brandonhippe/Indoor-Air-Quality-Monitor/Google Drive/Pin Definitions.docx

Unchangeable Pins:

- I2C_0 SCL: 9
- I2C_0 SDA: 10
- I2C_1 SCL: 14
- I2C_1 SDA: 15
- RX: 3
- TX: 4

Changeable Pins:

- PM_SLEEP_PIN: 6
- CO2_SLEEP_PIN: 7
- ANEM_SLEEP_PIN: 8
- ULTRASONIC_TRIG_1: 16
- ULTRASONIC_ECHO_1: 17
- ULTRASONIC_TRIG_2: 18
- ULTRASONIC_ECHO_2: 19
- Manny please put changeable smartmesh pins here

Notes:

- Sleep pins should have spots for transistors to turn off that sensor. Not likely to need them all, but probably nice to have
- Likely will need 2nd I2C bus for just CO2 sensor in order to properly put it to sleep without messing with other sensors on bus

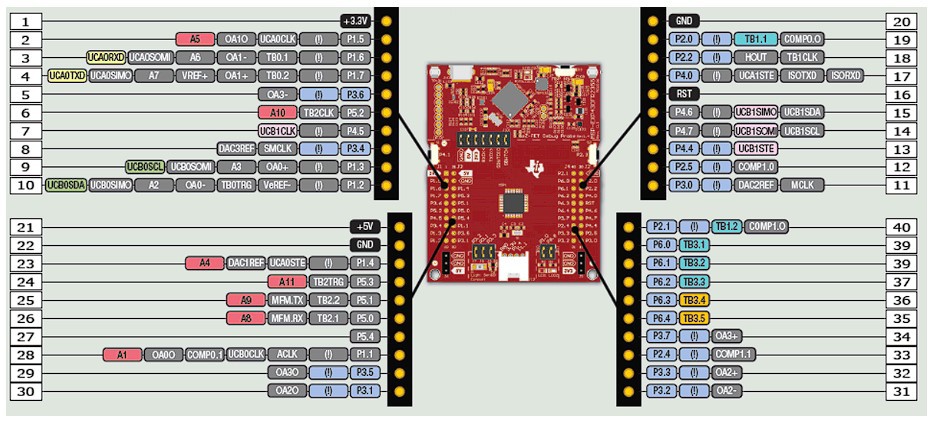
[picture p56: figure]
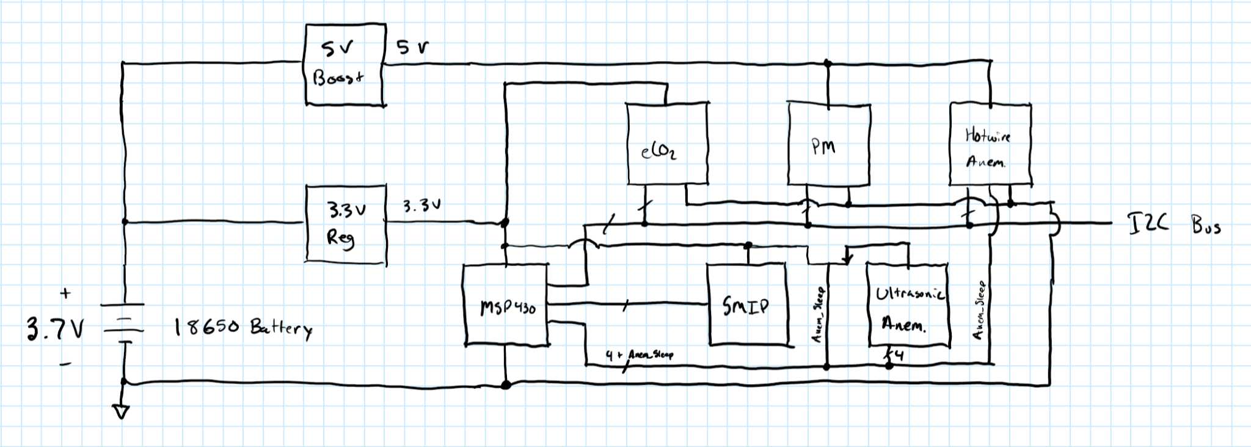
[picture p57: figure]
