brandonhippe/Indoor-Air-Quality-Monitor/Google Drive/Photos/COM port selected.png

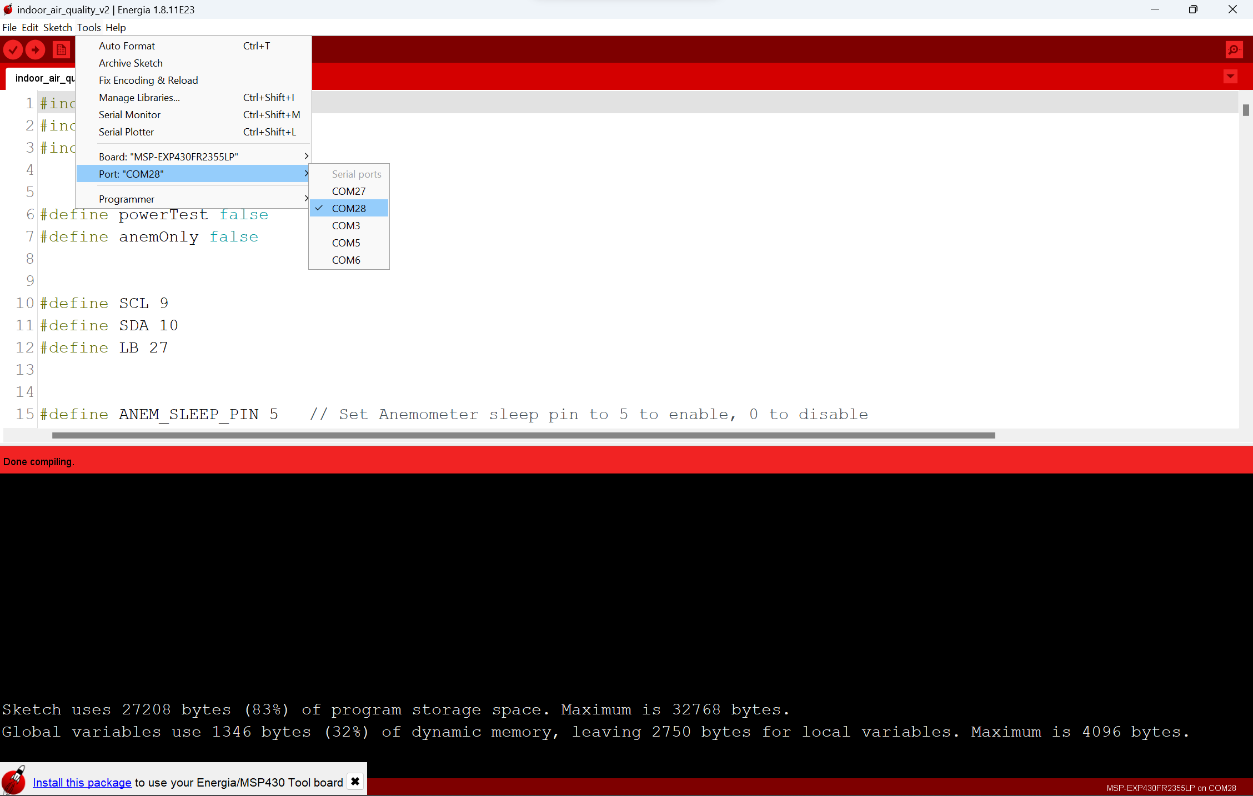
Google Drive/Photos/COM port selected.png
