brandonhippe/Indoor-Air-Quality-Monitor/Google Drive/Photos/device manager.png

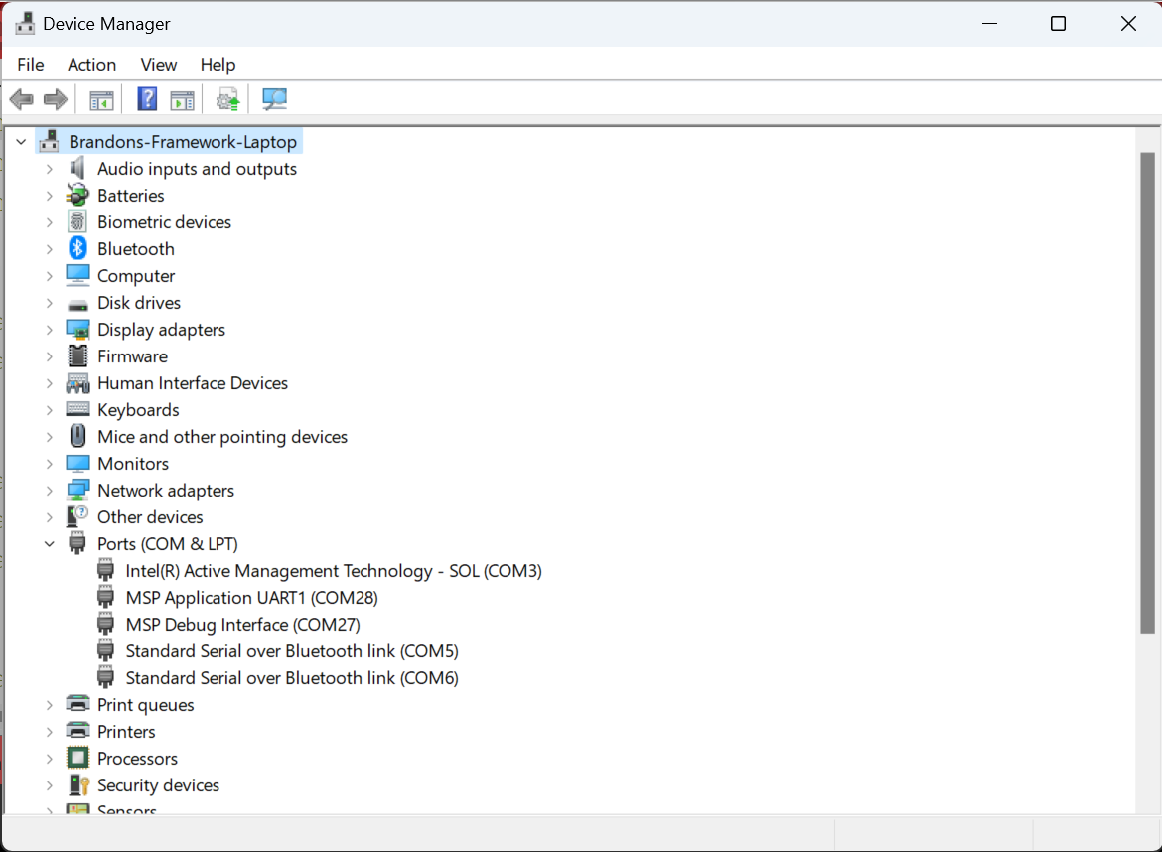
Google Drive/Photos/device manager.png
