brandonhippe/Indoor-Air-Quality-Monitor/Google Drive/Photos/Energia Started and board selected.png

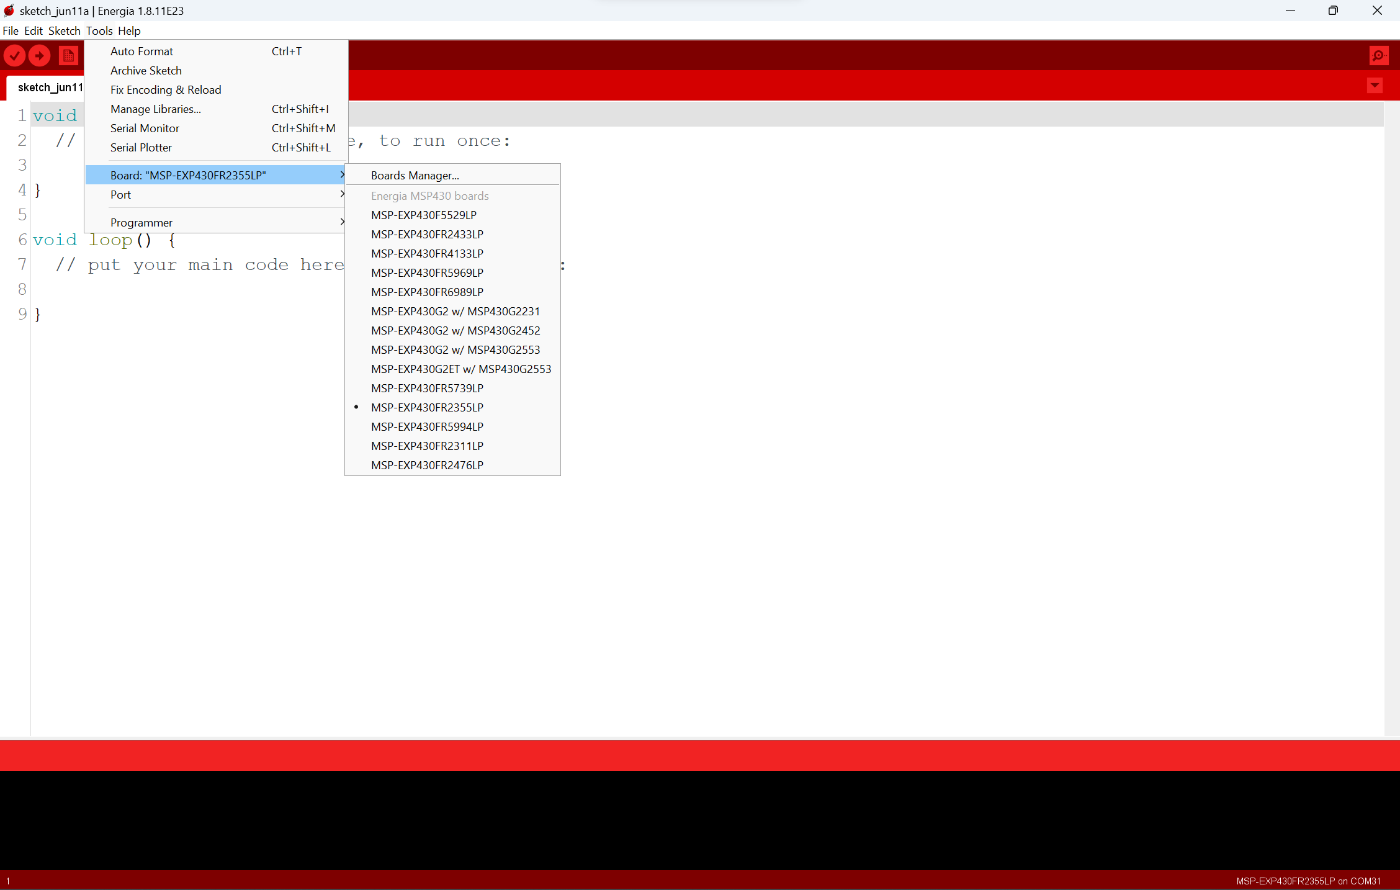
Google Drive/Photos/Energia Started and board selected.png
