brandonhippe/Indoor-Air-Quality-Monitor/Google Drive/Photos/Github Download.png

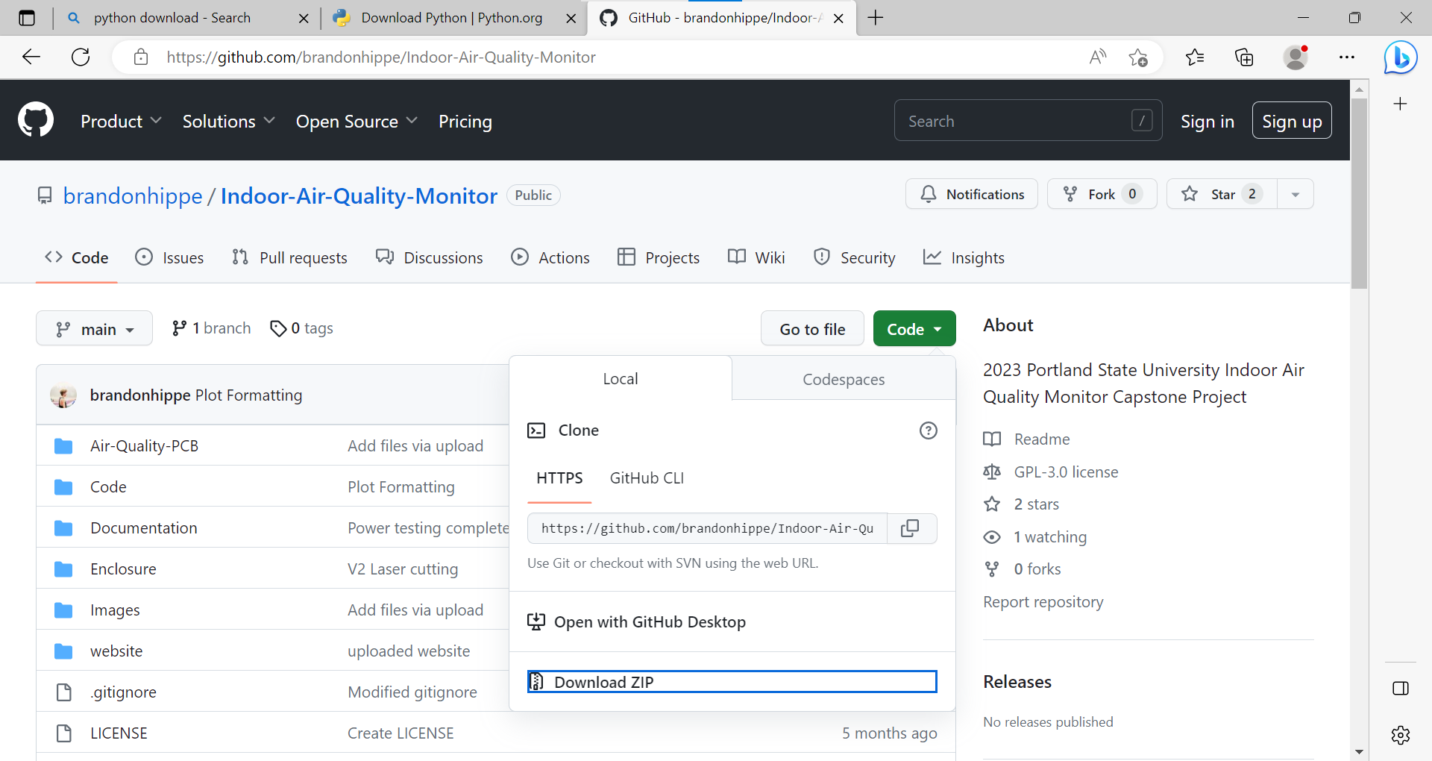
Google Drive/Photos/Github Download.png
