brandonhippe/Indoor-Air-Quality-Monitor/Google Drive/Photos/Libraries copied.png

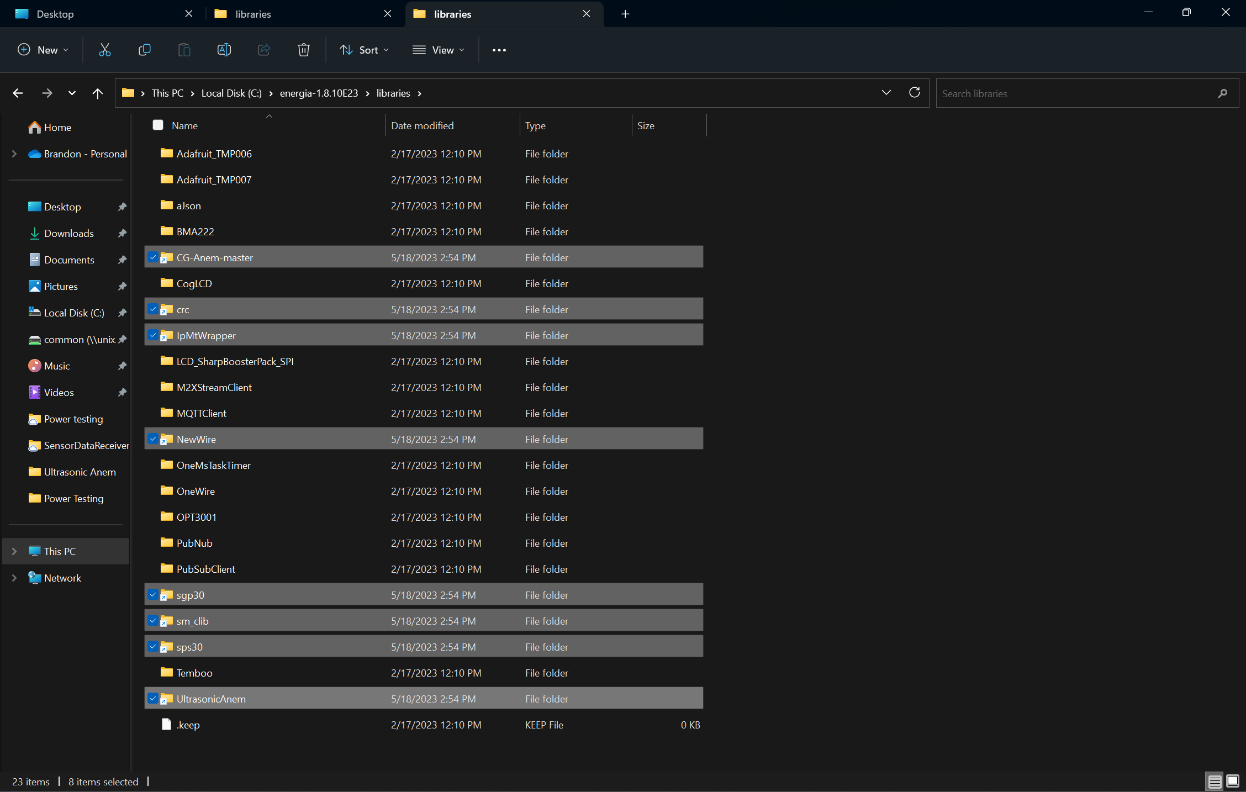
Google Drive/Photos/Libraries copied.png
