brandonhippe/Indoor-Air-Quality-Monitor/Google Drive/Photos/Libraries to copy.png

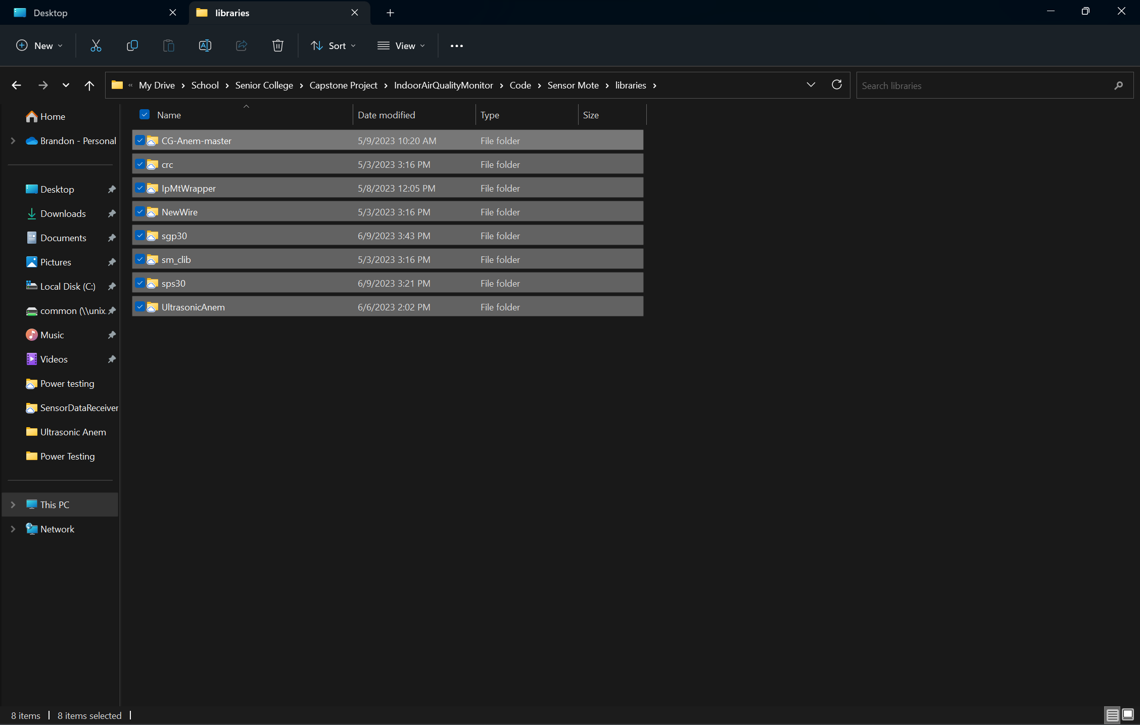
Google Drive/Photos/Libraries to copy.png
