brandonhippe/Indoor-Air-Quality-Monitor/Google Drive/Photos/Low Battery Alert.png

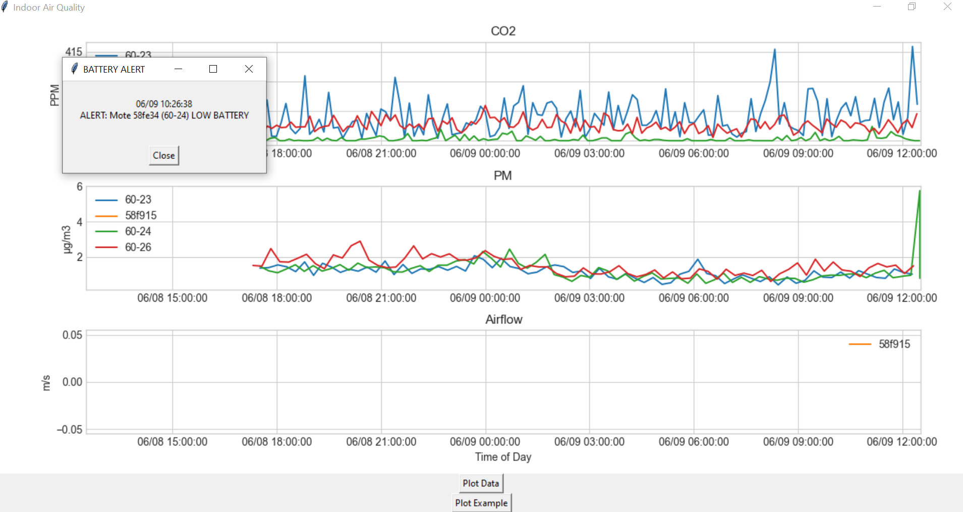
Google Drive/Photos/Low Battery Alert.png
