brandonhippe/Indoor-Air-Quality-Monitor/Google Drive/Photos/manager plugged in.png

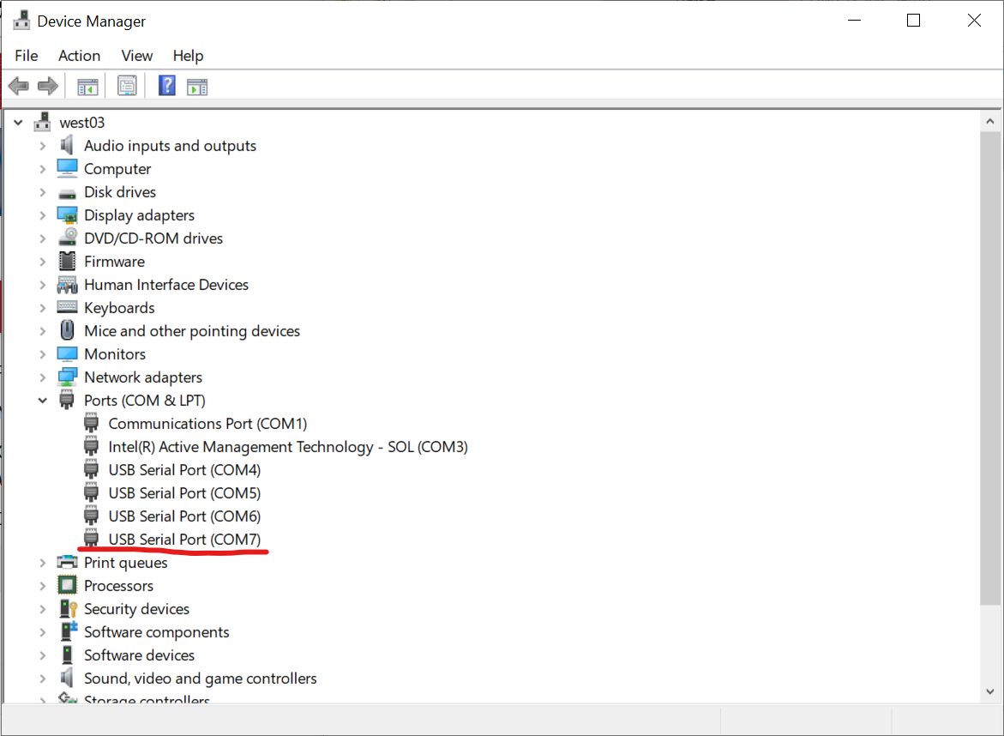
Google Drive/Photos/manager plugged in.png
