brandonhippe/Indoor-Air-Quality-Monitor/Google Drive/Photos/PXL_20230509_195835408.jpg

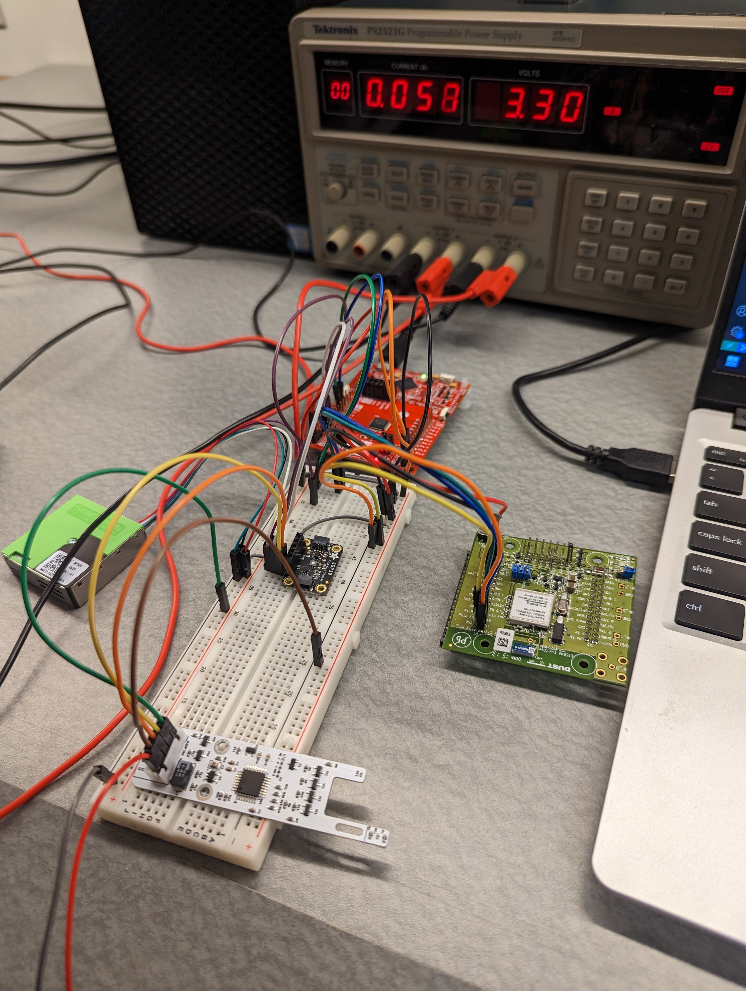
Google Drive/Photos/PXL_20230509_195835408.jpg
