brandonhippe/Indoor-Air-Quality-Monitor/Google Drive/Photos/PXL_20230510_175557905.jpg

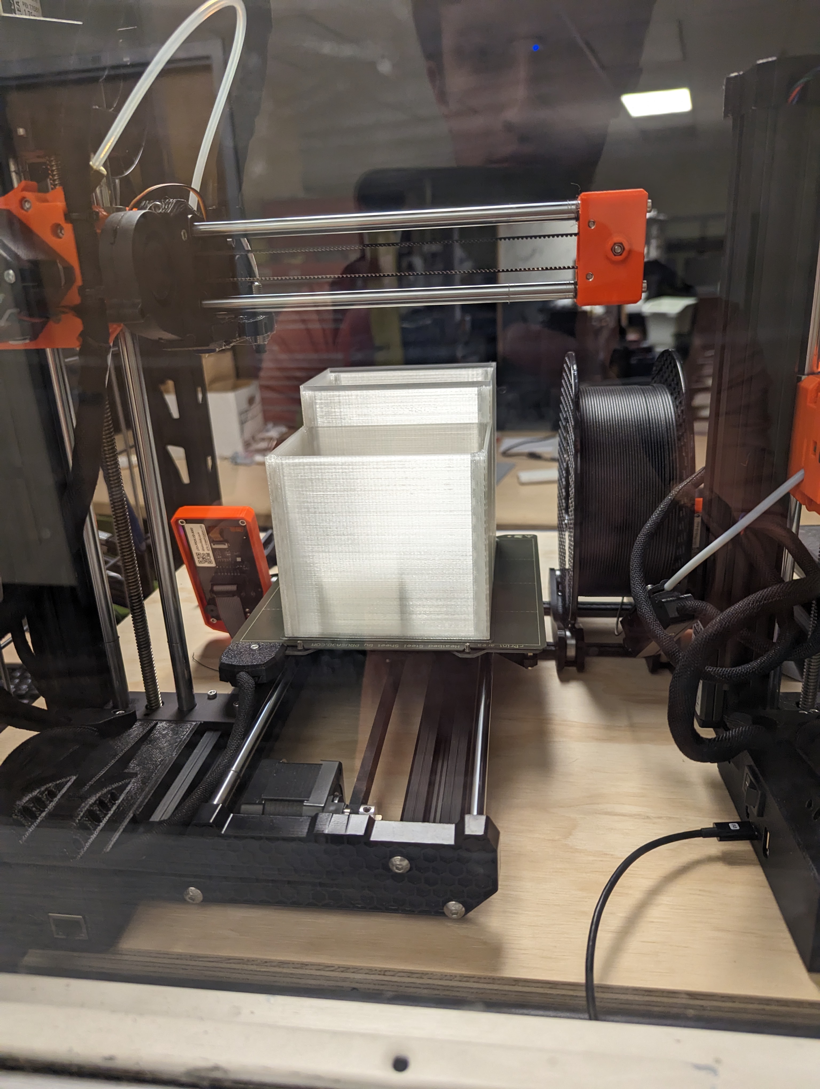
Google Drive/Photos/PXL_20230510_175557905.jpg
