brandonhippe/Indoor-Air-Quality-Monitor/Google Drive/Photos/PXL_20230510_200031936.jpg

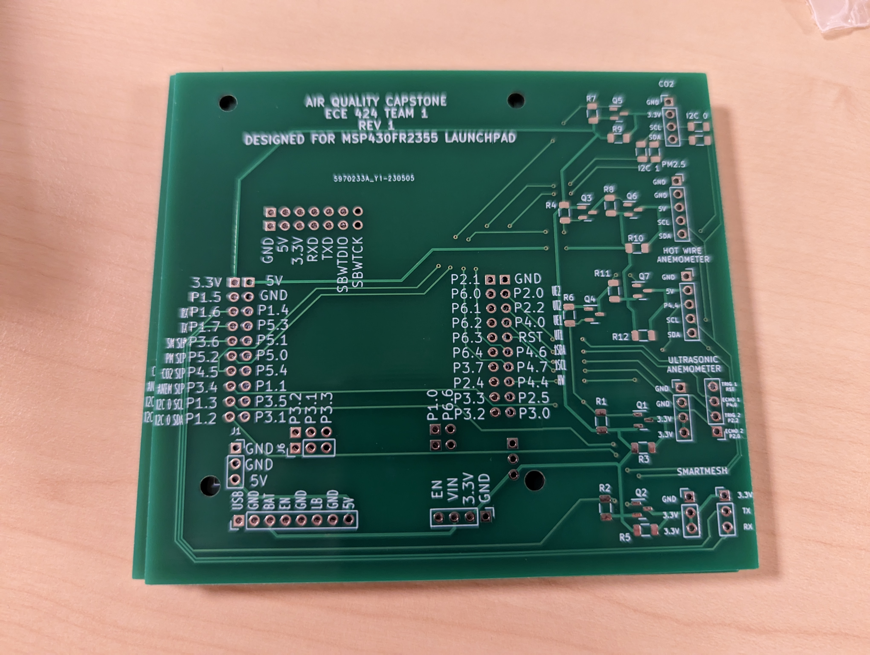
Google Drive/Photos/PXL_20230510_200031936.jpg
