brandonhippe/Indoor-Air-Quality-Monitor/Google Drive/Photos/PXL_20230516_212648805.jpg

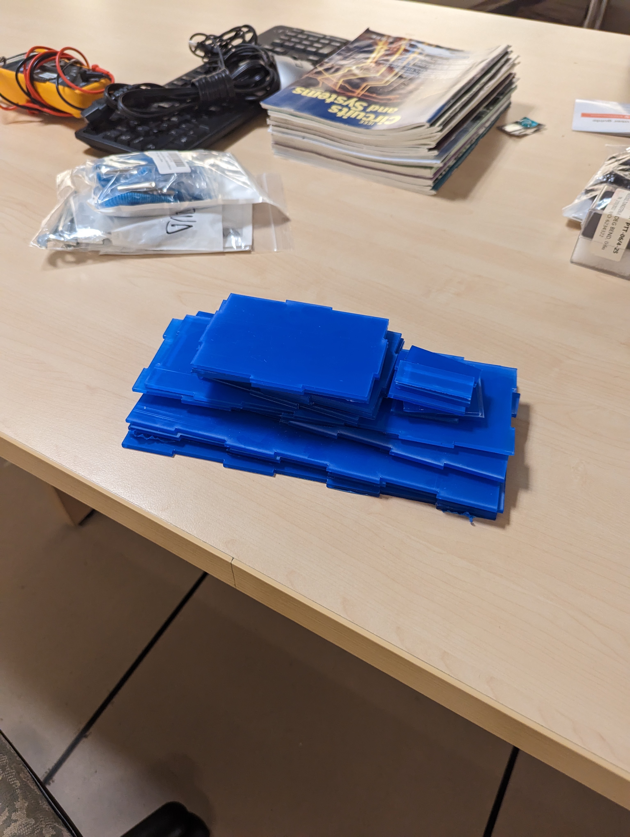
Google Drive/Photos/PXL_20230516_212648805.jpg
