brandonhippe/Indoor-Air-Quality-Monitor/Google Drive/Photos/PXL_20230516_223832451.jpg

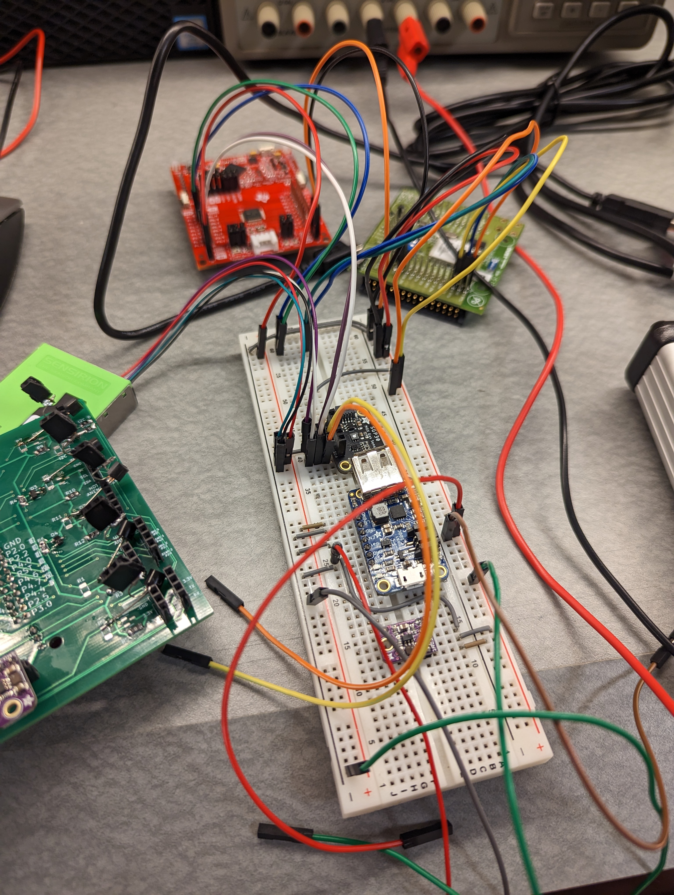
Google Drive/Photos/PXL_20230516_223832451.jpg
