brandonhippe/Indoor-Air-Quality-Monitor/Google Drive/Photos/PXL_20230524_002447540.jpg

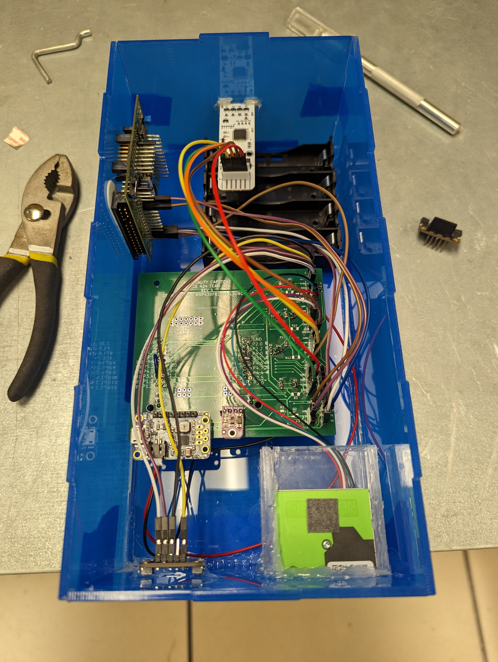
Google Drive/Photos/PXL_20230524_002447540.jpg
