brandonhippe/Indoor-Air-Quality-Monitor/Google Drive/Photos/PXL_20230524_012021392.jpg

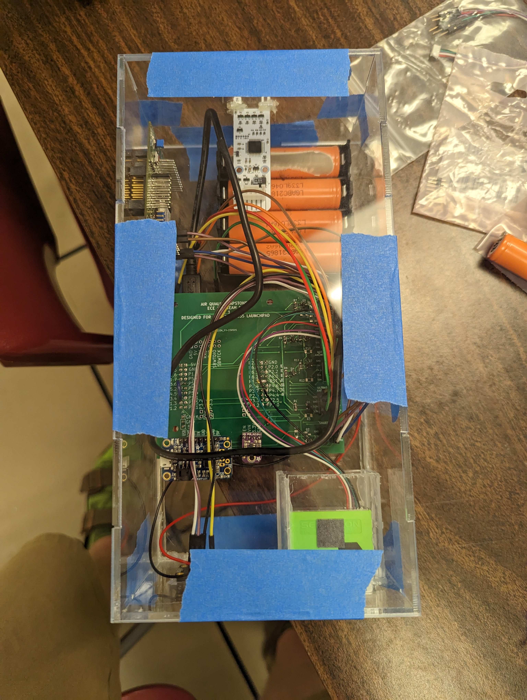
Google Drive/Photos/PXL_20230524_012021392.jpg
