brandonhippe/Indoor-Air-Quality-Monitor/Google Drive/Photos/PXL_20230524_172544205.jpg

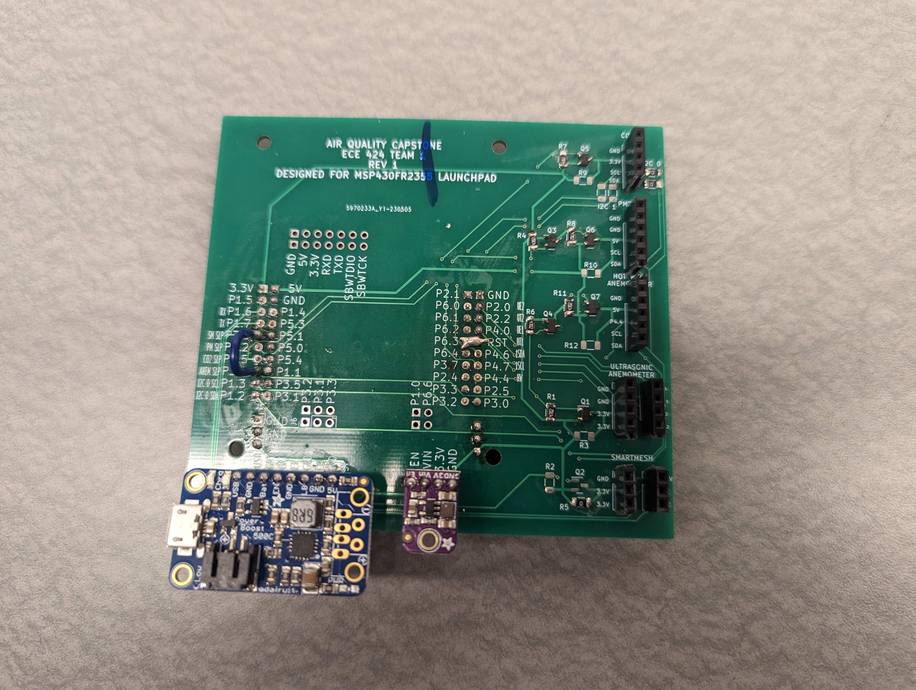
Google Drive/Photos/PXL_20230524_172544205.jpg
