brandonhippe/Indoor-Air-Quality-Monitor/Google Drive/Photos/PXL_20230524_172617568.jpg

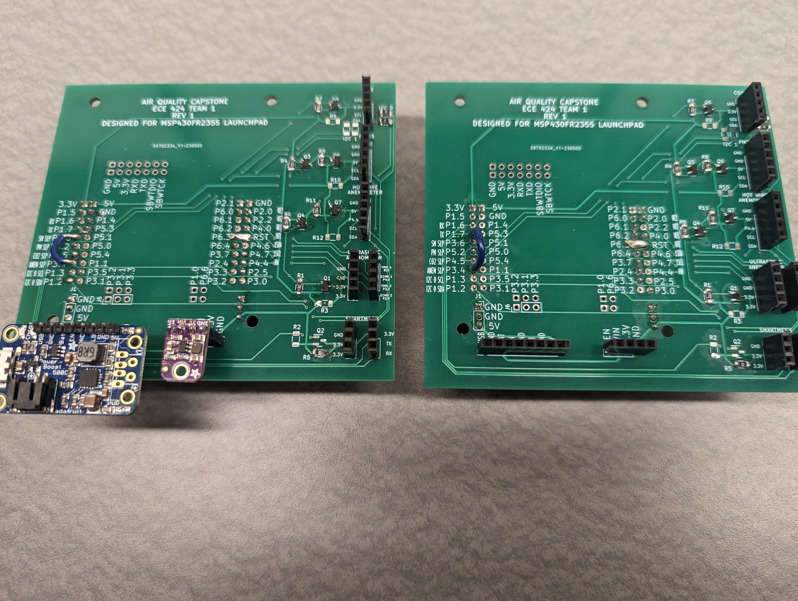
Google Drive/Photos/PXL_20230524_172617568.jpg
