brandonhippe/Indoor-Air-Quality-Monitor/Google Drive/Photos/PXL_20230524_172642097.jpg

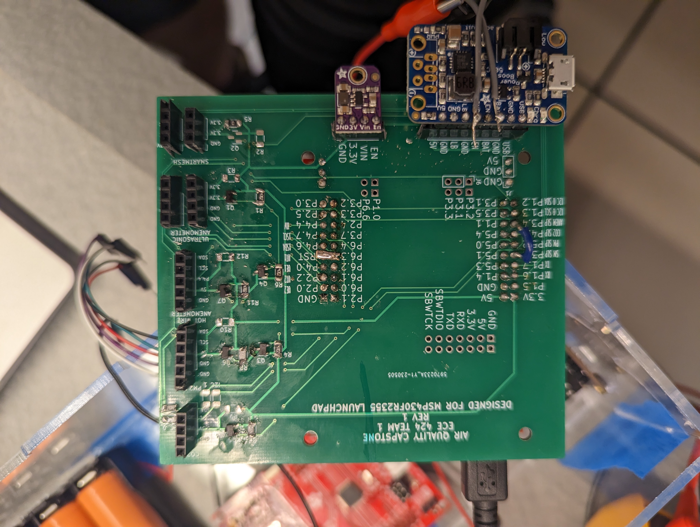
Google Drive/Photos/PXL_20230524_172642097.jpg
