brandonhippe/Indoor-Air-Quality-Monitor/Google Drive/Photos/PXL_20230602_221326991.jpg

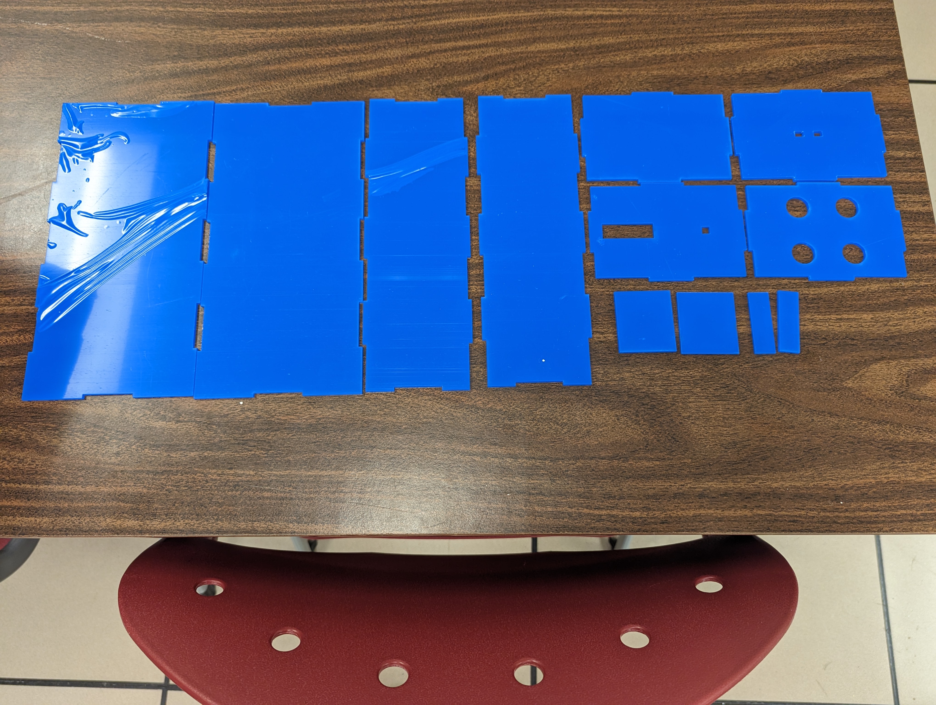
Google Drive/Photos/PXL_20230602_221326991.jpg
