brandonhippe/Indoor-Air-Quality-Monitor/Google Drive/Photos/PXL_20230602_222331544.jpg

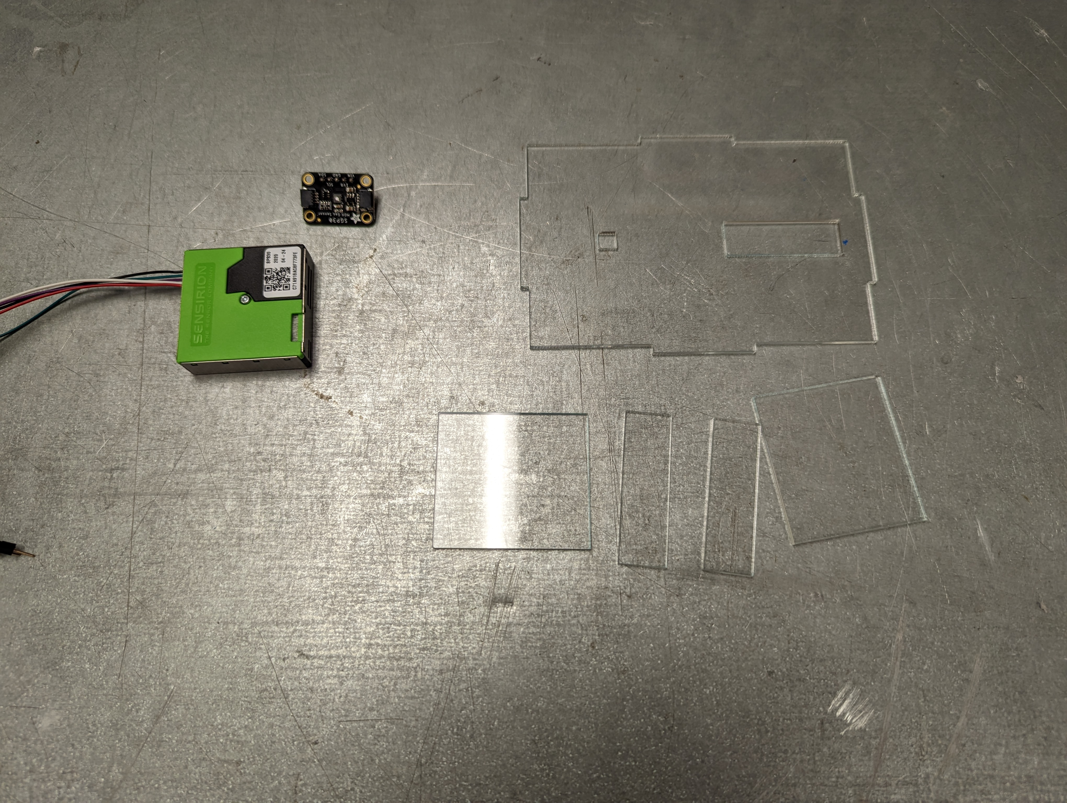
Google Drive/Photos/PXL_20230602_222331544.jpg
