brandonhippe/Indoor-Air-Quality-Monitor/Google Drive/Photos/PXL_20230602_222806239.jpg

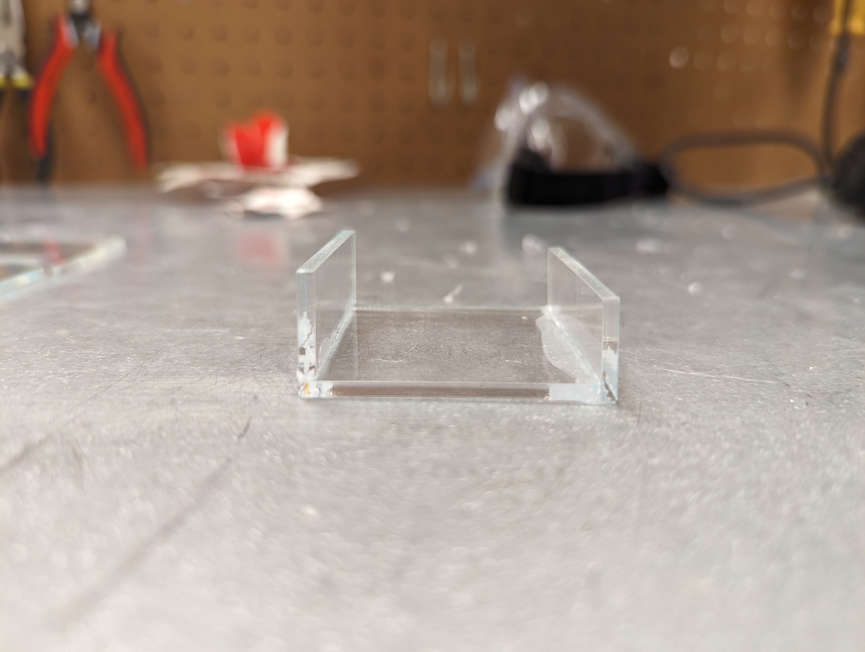
Google Drive/Photos/PXL_20230602_222806239.jpg
