brandonhippe/Indoor-Air-Quality-Monitor/Google Drive/Photos/PXL_20230602_222922491.jpg

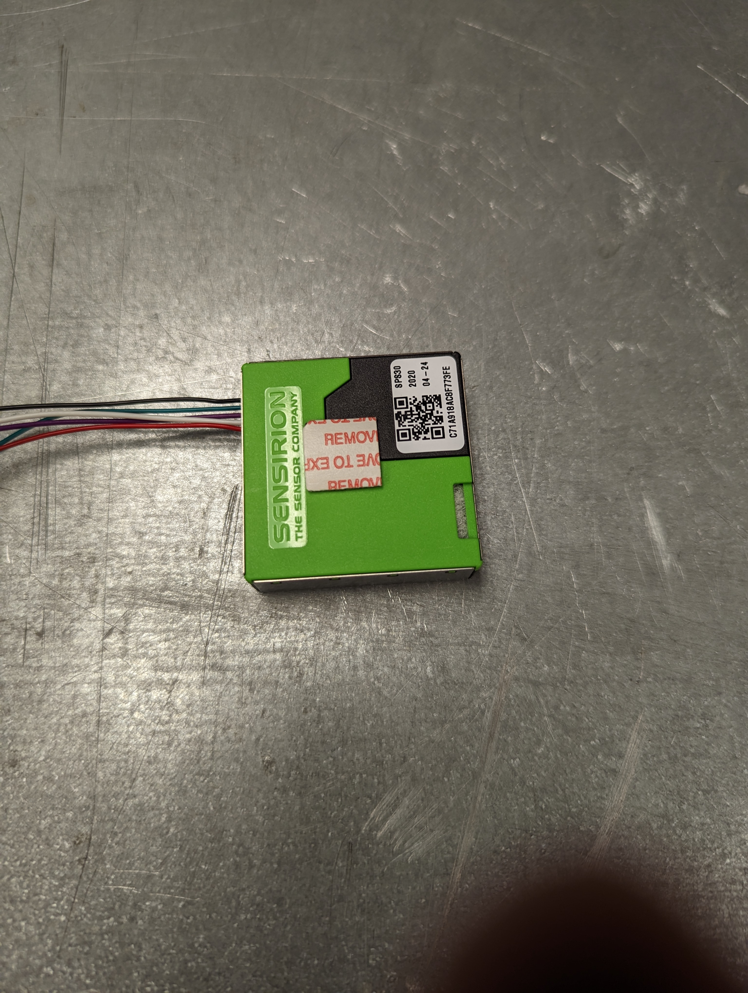
Google Drive/Photos/PXL_20230602_222922491.jpg
