brandonhippe/Indoor-Air-Quality-Monitor/Google Drive/Photos/PXL_20230602_223028937.jpg

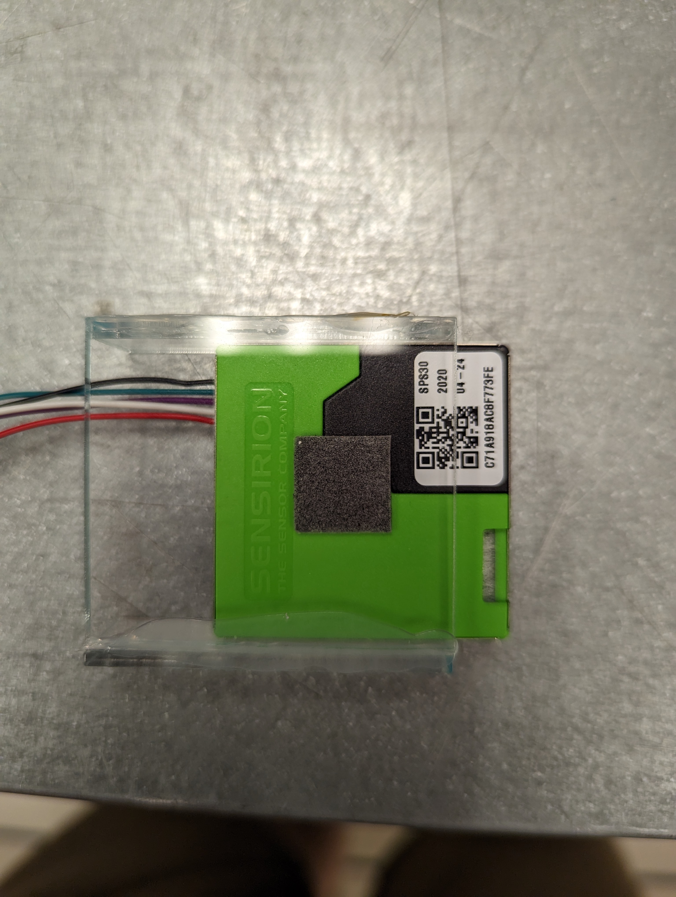
Google Drive/Photos/PXL_20230602_223028937.jpg
