brandonhippe/Indoor-Air-Quality-Monitor/Google Drive/Photos/PXL_20230602_223123664.jpg

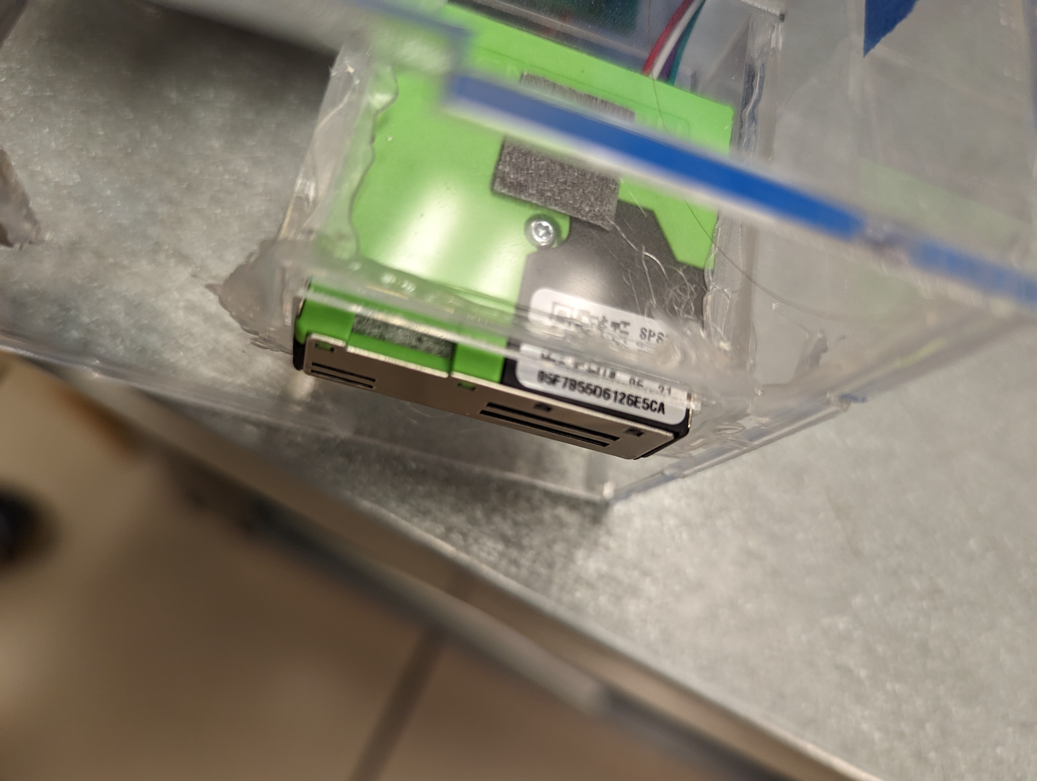
Google Drive/Photos/PXL_20230602_223123664.jpg
