brandonhippe/Indoor-Air-Quality-Monitor/Google Drive/Photos/PXL_20230602_223311003.jpg

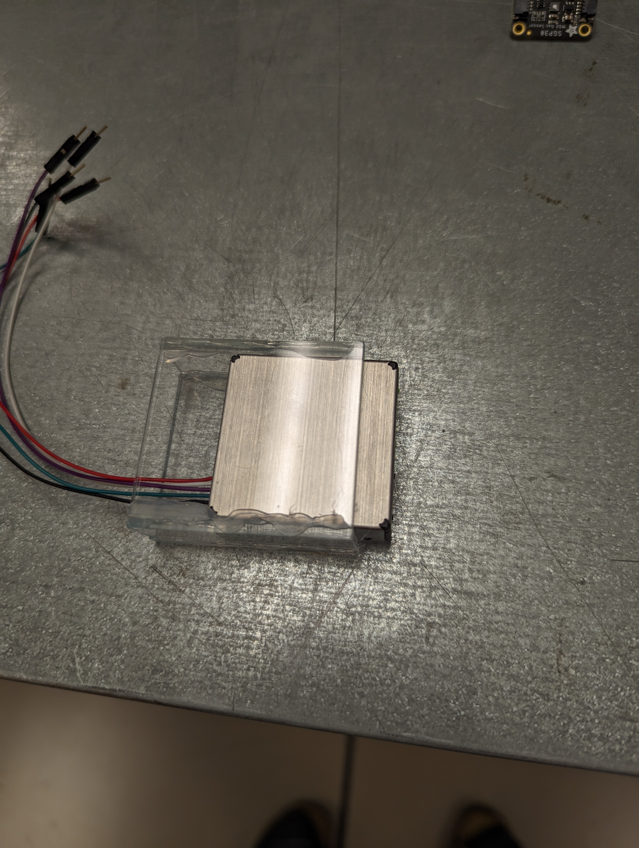
Google Drive/Photos/PXL_20230602_223311003.jpg
