brandonhippe/Indoor-Air-Quality-Monitor/Google Drive/Photos/PXL_20230602_223421171.jpg

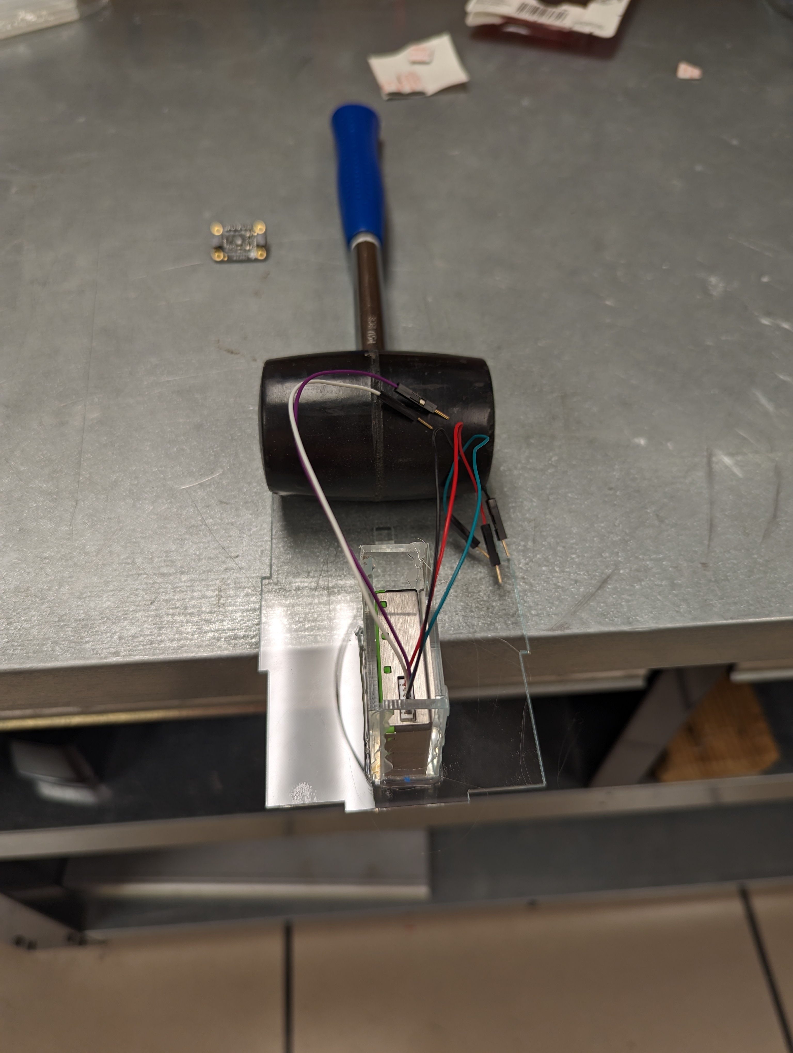
Google Drive/Photos/PXL_20230602_223421171.jpg
