brandonhippe/Indoor-Air-Quality-Monitor/Google Drive/Photos/PXL_20230602_223711670.jpg

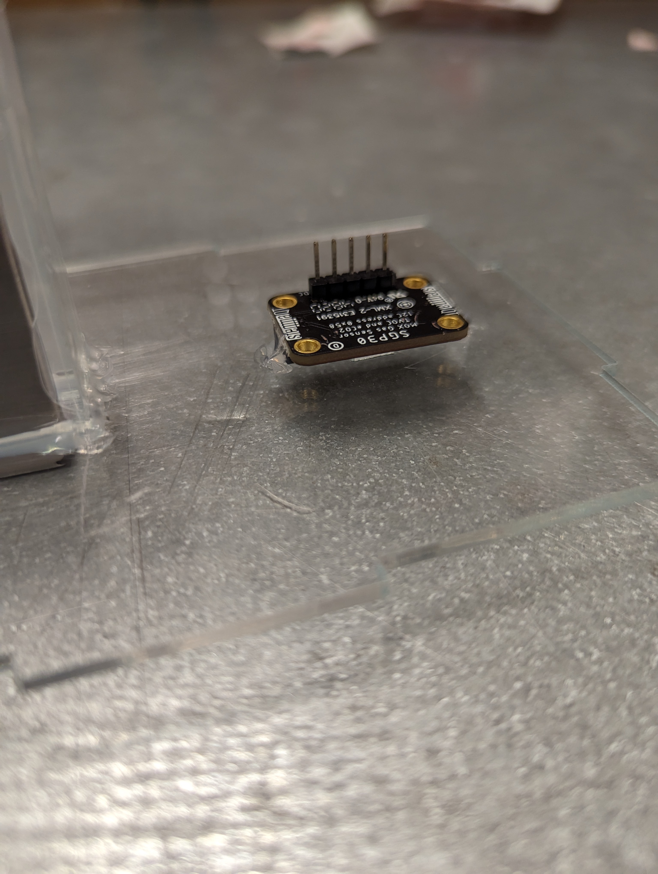
Google Drive/Photos/PXL_20230602_223711670.jpg
