brandonhippe/Indoor-Air-Quality-Monitor/Google Drive/Photos/PXL_20230602_223719457.jpg

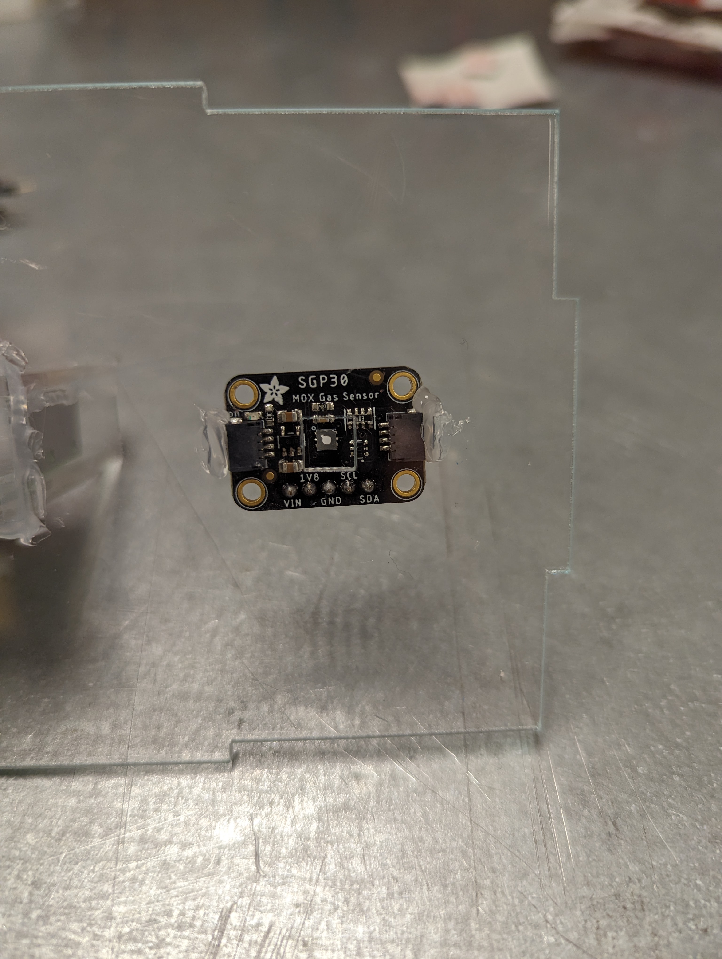
Google Drive/Photos/PXL_20230602_223719457.jpg
