brandonhippe/Indoor-Air-Quality-Monitor/Google Drive/Photos/PXL_20230602_224345984.jpg

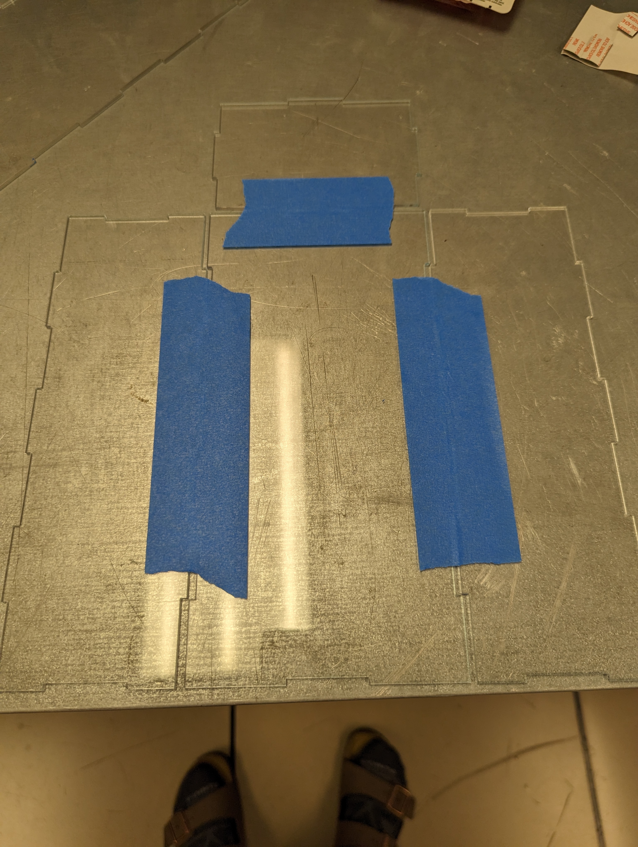
Google Drive/Photos/PXL_20230602_224345984.jpg
