brandonhippe/Indoor-Air-Quality-Monitor/Google Drive/Photos/PXL_20230602_224513106.jpg

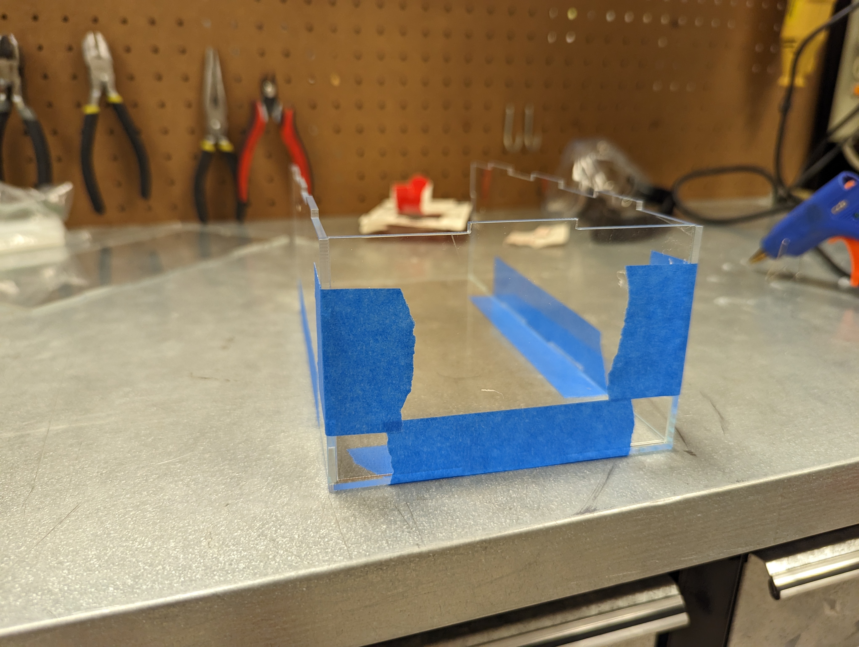
Google Drive/Photos/PXL_20230602_224513106.jpg
