brandonhippe/Indoor-Air-Quality-Monitor/Google Drive/Photos/PXL_20230602_225319473.jpg

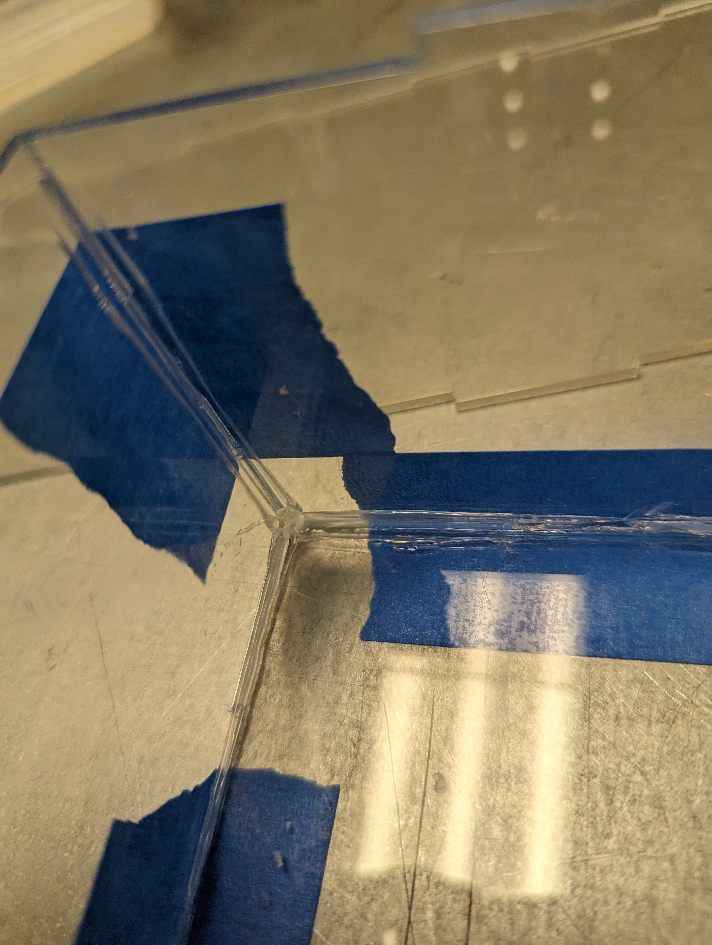
Google Drive/Photos/PXL_20230602_225319473.jpg
