brandonhippe/Indoor-Air-Quality-Monitor/Google Drive/Photos/PXL_20230602_225957423.jpg

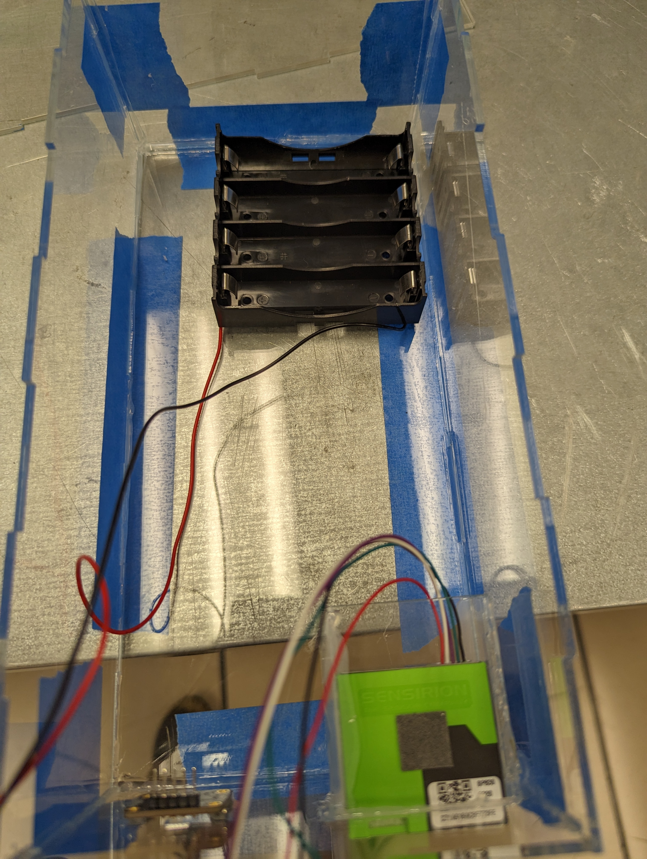
Google Drive/Photos/PXL_20230602_225957423.jpg
