brandonhippe/Indoor-Air-Quality-Monitor/Google Drive/Photos/PXL_20230602_230428449.jpg

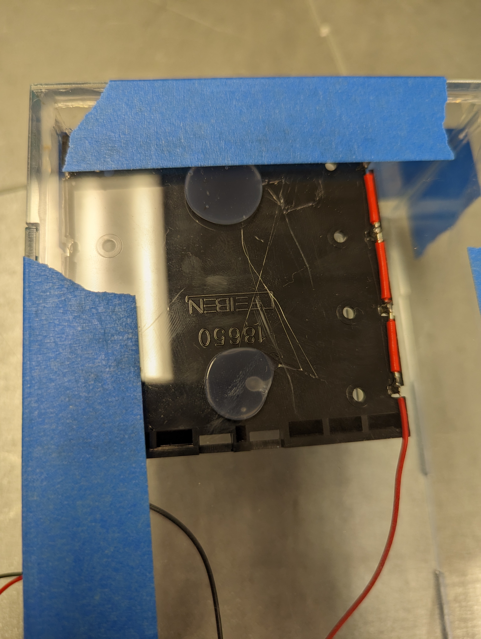
Google Drive/Photos/PXL_20230602_230428449.jpg
