brandonhippe/Indoor-Air-Quality-Monitor/Google Drive/Photos/PXL_20230602_230817055.jpg

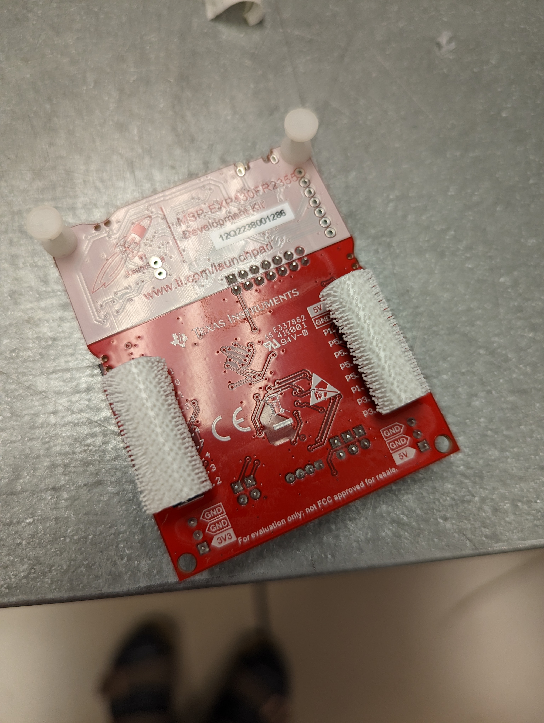
Google Drive/Photos/PXL_20230602_230817055.jpg
