brandonhippe/Indoor-Air-Quality-Monitor/Google Drive/Photos/PXL_20230602_230912100.jpg

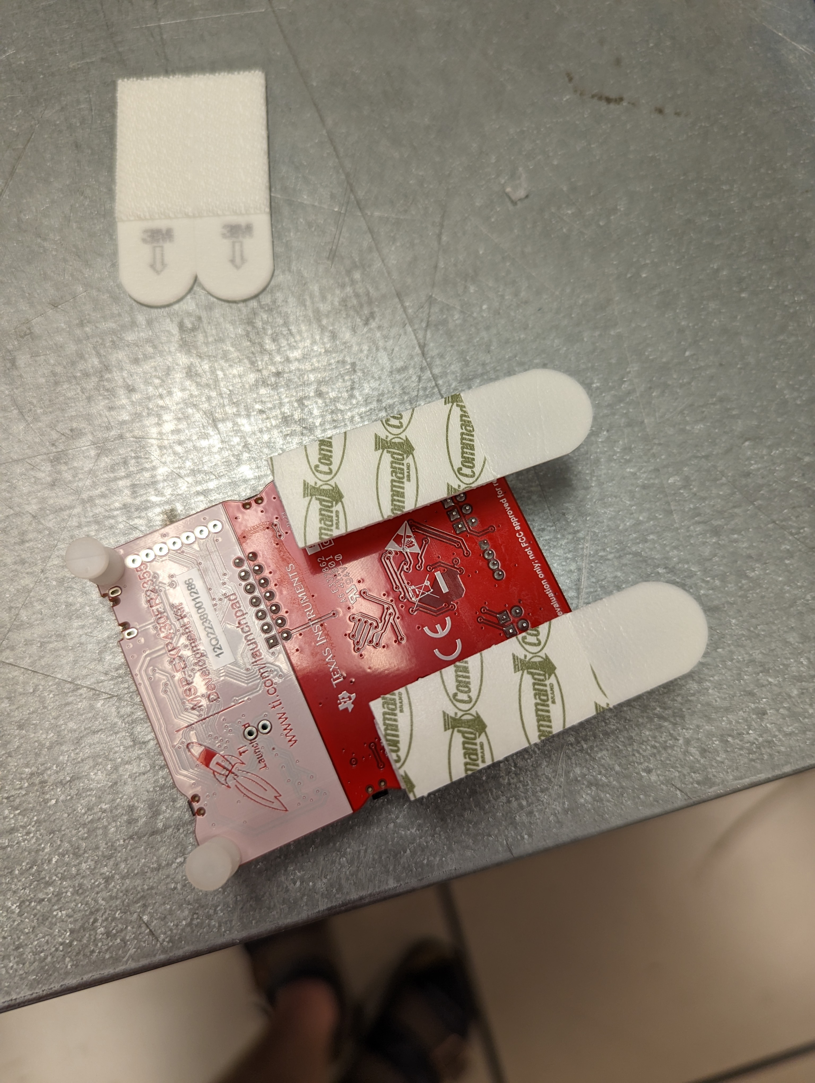
Google Drive/Photos/PXL_20230602_230912100.jpg
