brandonhippe/Indoor-Air-Quality-Monitor/Google Drive/Photos/PXL_20230602_231155861.jpg

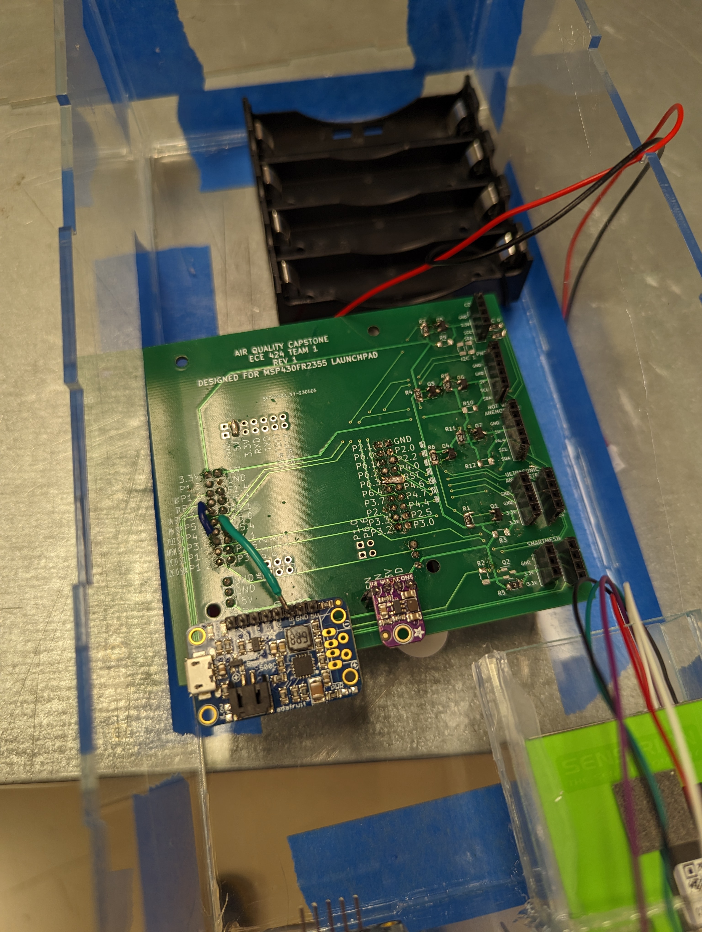
Google Drive/Photos/PXL_20230602_231155861.jpg
