brandonhippe/Indoor-Air-Quality-Monitor/Google Drive/Photos/PXL_20230602_231438738.jpg

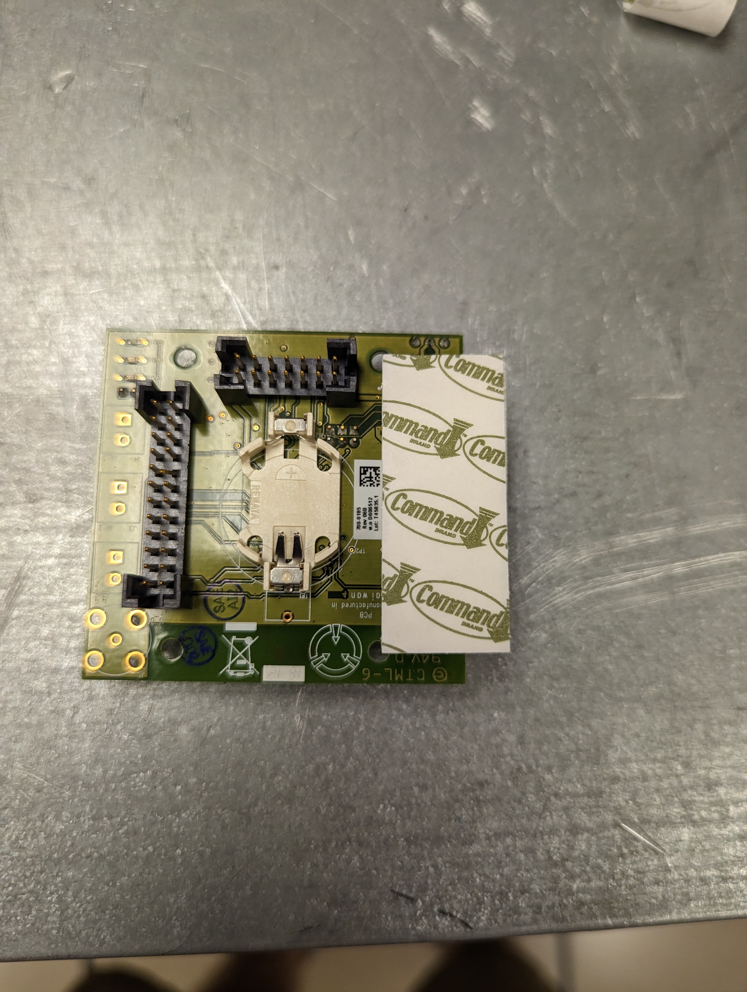
Google Drive/Photos/PXL_20230602_231438738.jpg
