brandonhippe/Indoor-Air-Quality-Monitor/Google Drive/Photos/PXL_20230602_231850344.jpg

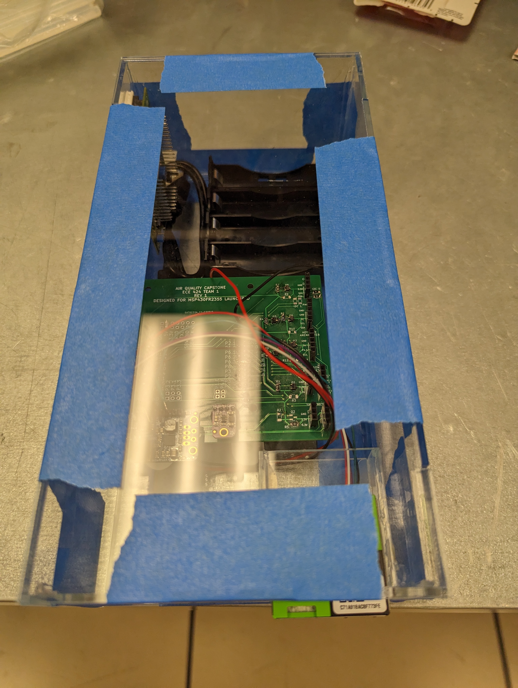
Google Drive/Photos/PXL_20230602_231850344.jpg
