brandonhippe/Indoor-Air-Quality-Monitor/Google Drive/Photos/PXL_20230603_182551021.jpg

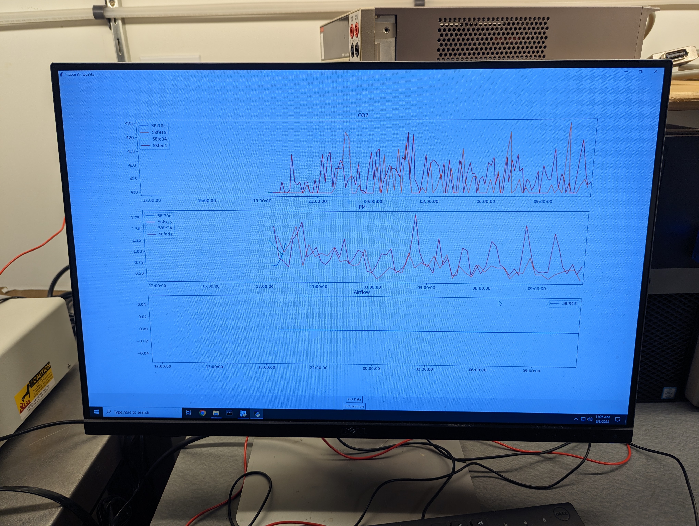
Google Drive/Photos/PXL_20230603_182551021.jpg
