brandonhippe/Indoor-Air-Quality-Monitor/Google Drive/Photos/PXL_20230609_004725791.jpg

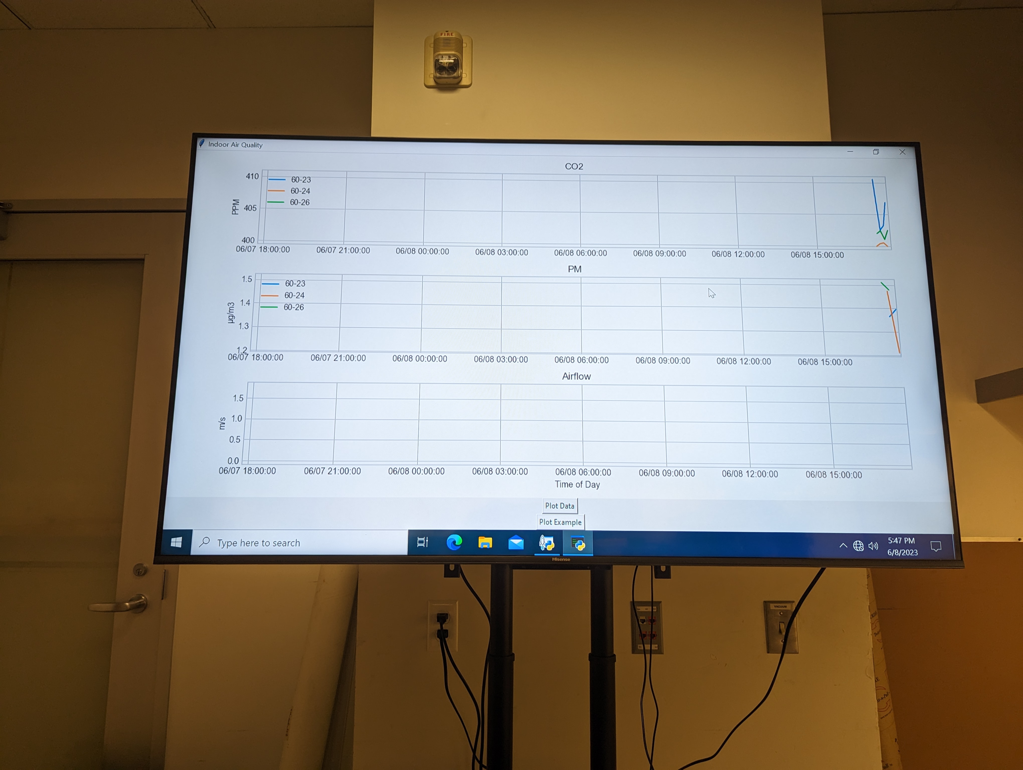
Google Drive/Photos/PXL_20230609_004725791.jpg
