brandonhippe/Indoor-Air-Quality-Monitor/Google Drive/Photos/PXL_20230611_001636522.jpg

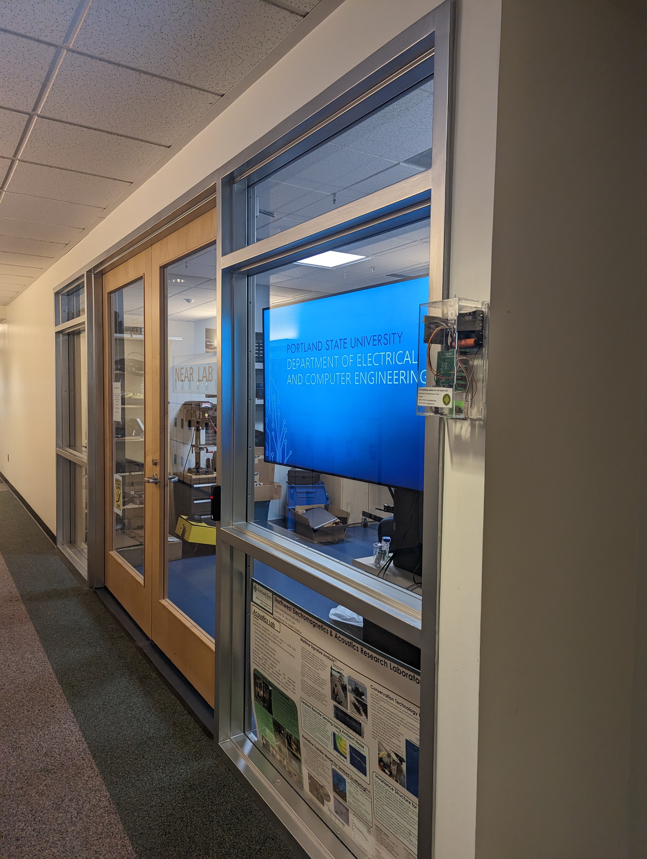
Google Drive/Photos/PXL_20230611_001636522.jpg
