brandonhippe/Indoor-Air-Quality-Monitor/Google Drive/Photos/PXL_20230611_001639559.jpg

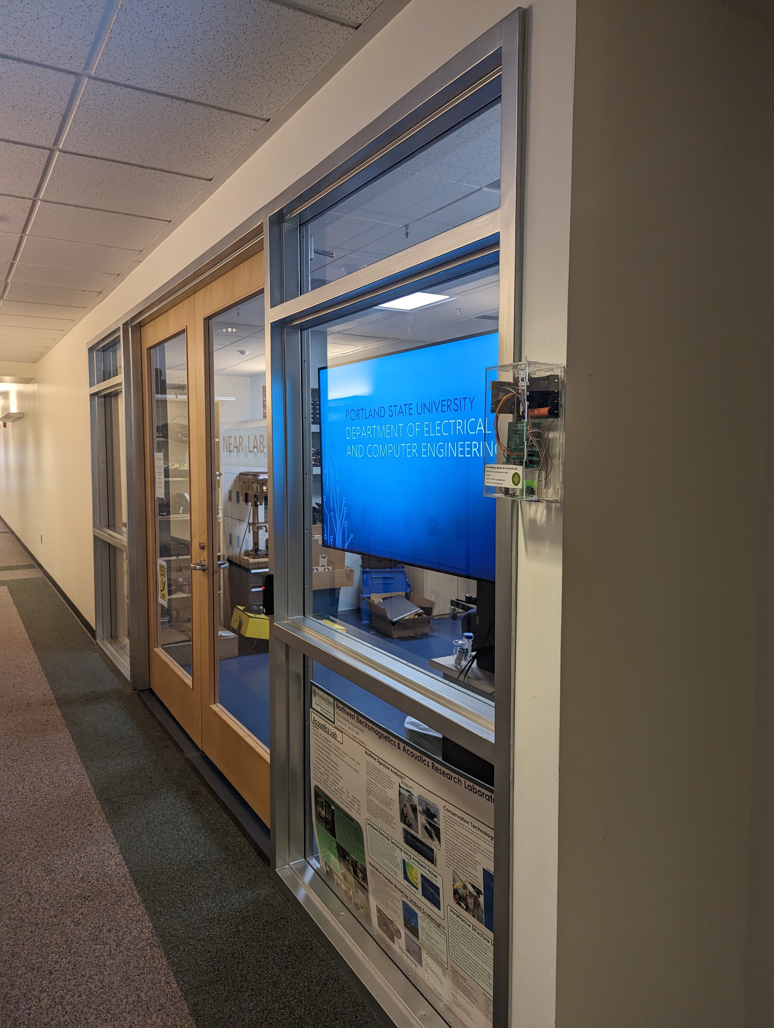
Google Drive/Photos/PXL_20230611_001639559.jpg
