brandonhippe/Indoor-Air-Quality-Monitor/Google Drive/Photos/PXL_20230611_001958449.jpg

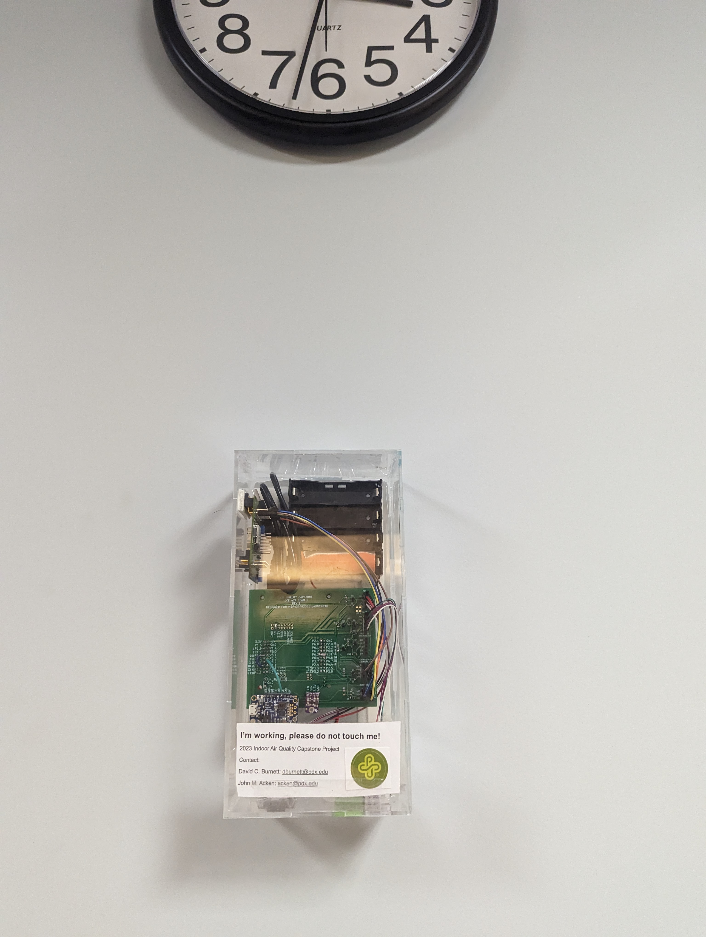
Google Drive/Photos/PXL_20230611_001958449.jpg
