brandonhippe/Indoor-Air-Quality-Monitor/Google Drive/Photos/PXL_20230611_002017217.jpg

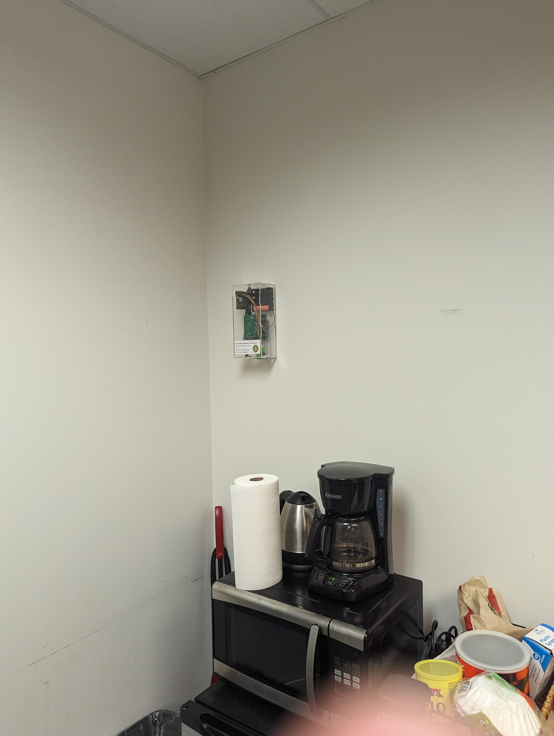
Google Drive/Photos/PXL_20230611_002017217.jpg
