brandonhippe/Indoor-Air-Quality-Monitor/Google Drive/Photos/PXL_20230611_002100109.jpg

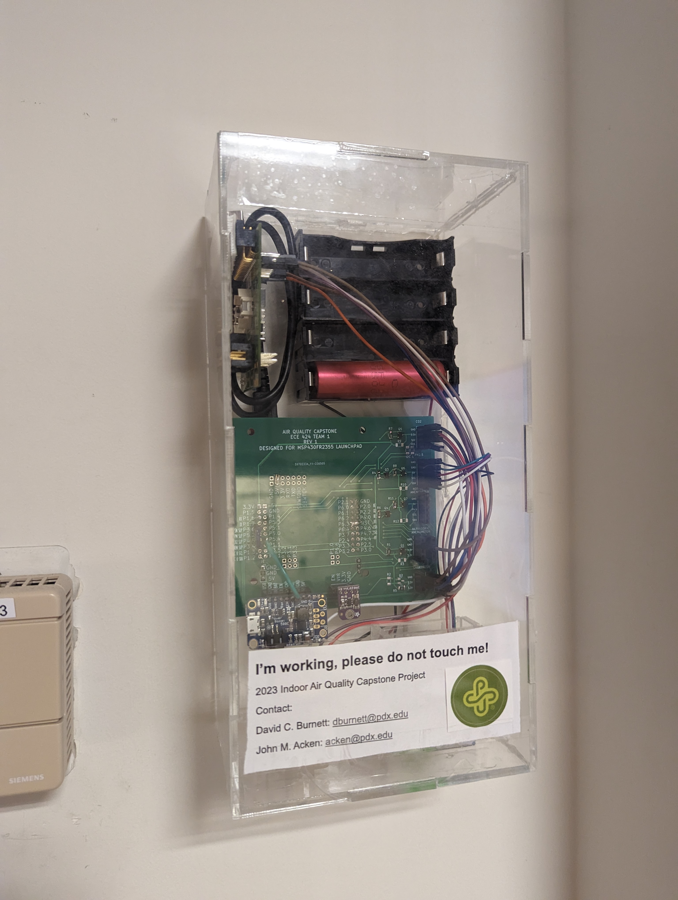
Google Drive/Photos/PXL_20230611_002100109.jpg
