brandonhippe/Indoor-Air-Quality-Monitor/Google Drive/Photos/serial monitor button.png

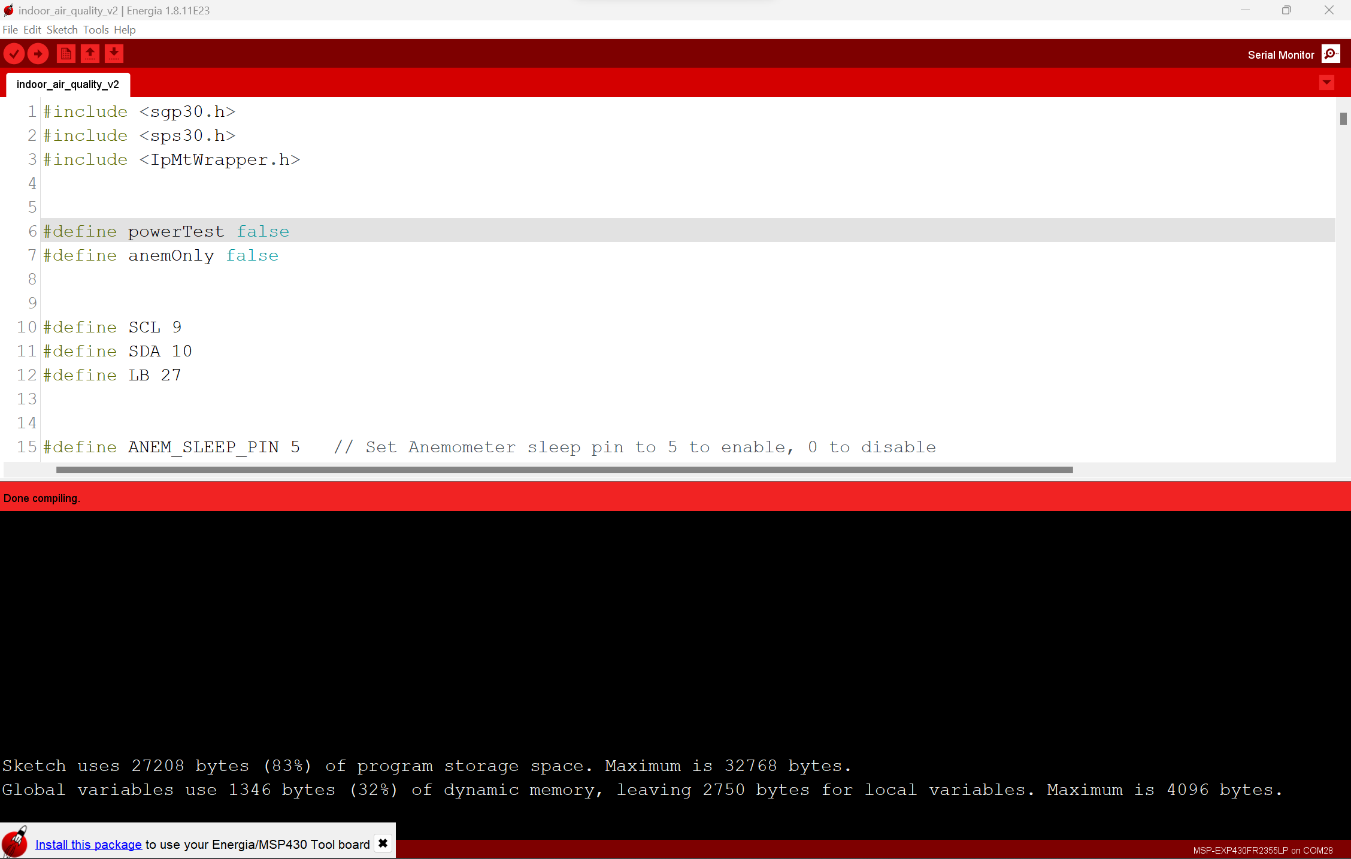
Google Drive/Photos/serial monitor button.png
