brandonhippe/Indoor-Air-Quality-Monitor/Google Drive/website/PICS/acken.png

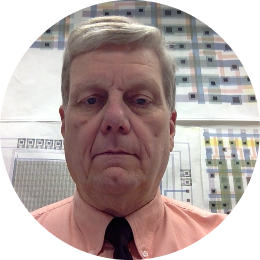
Google Drive/website/PICS/acken.png
