brandonhippe/Indoor-Air-Quality-Monitor/Google Drive/website/PICS/background.jpg

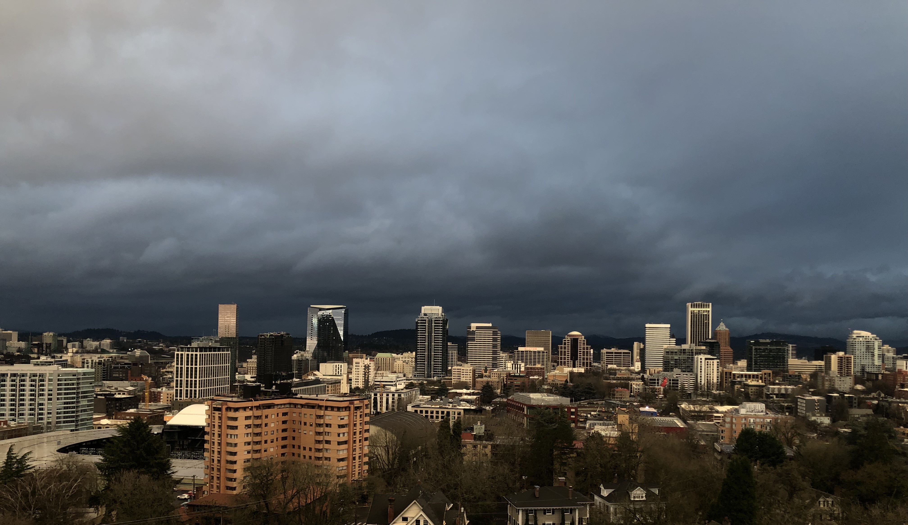
Google Drive/website/PICS/background.jpg
