brandonhippe/Indoor-Air-Quality-Monitor/Google Drive/website/PICS/burnett.png

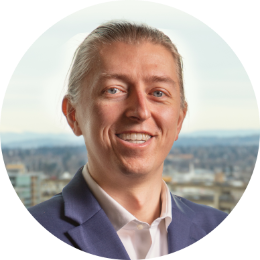
Google Drive/website/PICS/burnett.png
