brandonhippe/Indoor-Air-Quality-Monitor/Google Drive/website/PICS/circuit.jpg

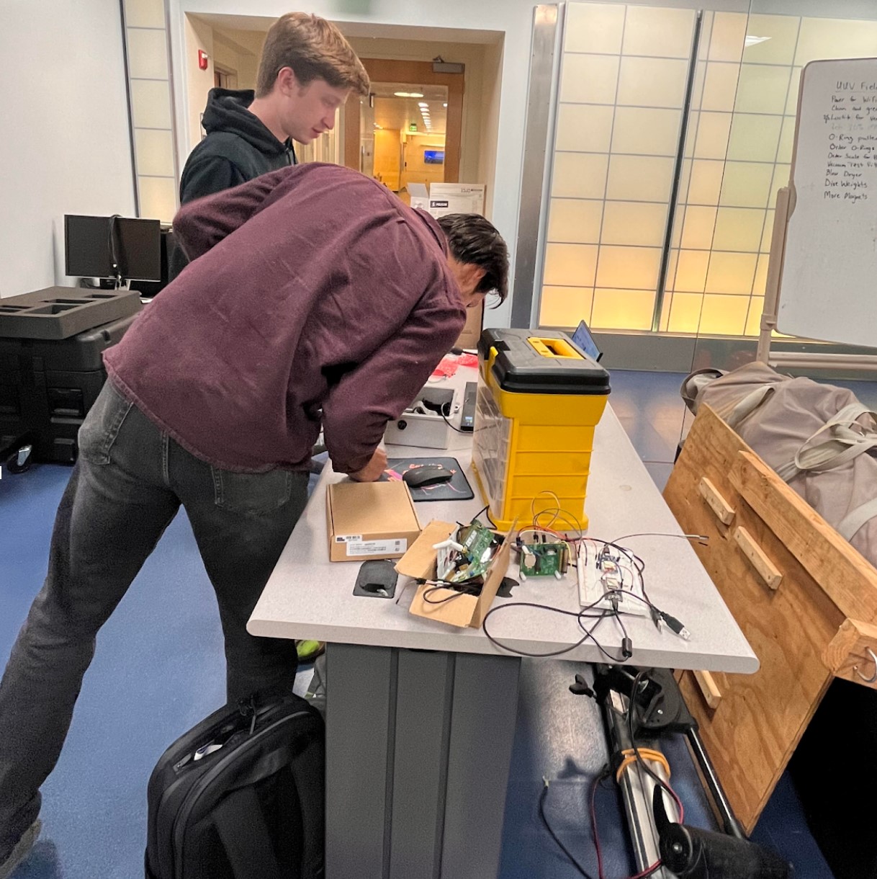
Google Drive/website/PICS/circuit.jpg
