brandonhippe/Indoor-Air-Quality-Monitor/Google Drive/website/PICS/final.jpg

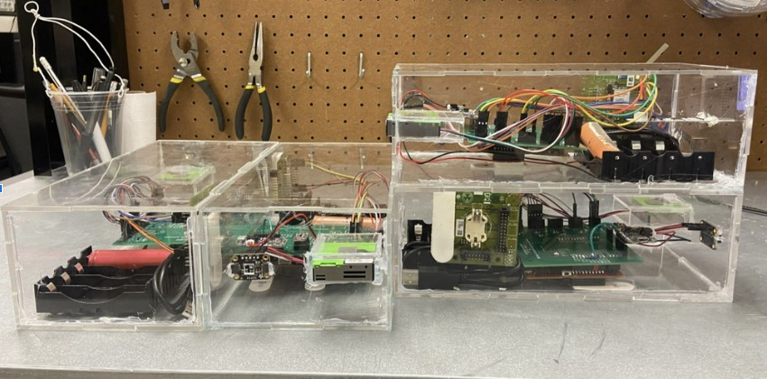
Google Drive/website/PICS/final.jpg
