brandonhippe/Indoor-Air-Quality-Monitor/Google Drive/website/PICS/L1diagram.jpg

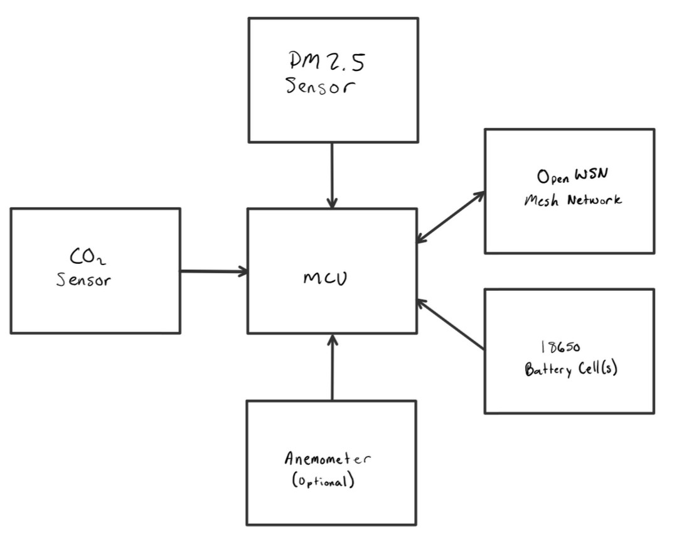
Google Drive/website/PICS/L1diagram.jpg
