brandonhippe/Indoor-Air-Quality-Monitor/Google Drive/website/PICS/oldproject.jpg

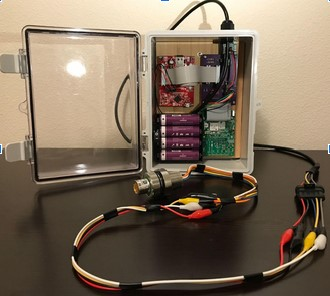
Google Drive/website/PICS/oldproject.jpg
