brandonhippe/Indoor-Air-Quality-Monitor/Google Drive/website/PICS/student.png

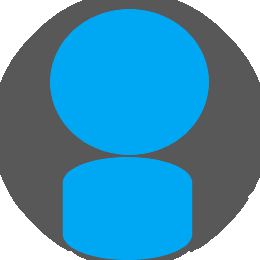
Google Drive/website/PICS/student.png
