brandonhippe/Indoor-Air-Quality-Monitor/Google Drive/website/PICS/topview.jpg

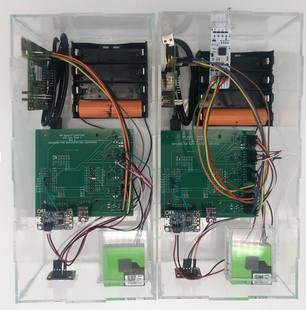
Google Drive/website/PICS/topview.jpg
