brandonhippe/Indoor-Air-Quality-Monitor/Images/L1diagramP2.jpg

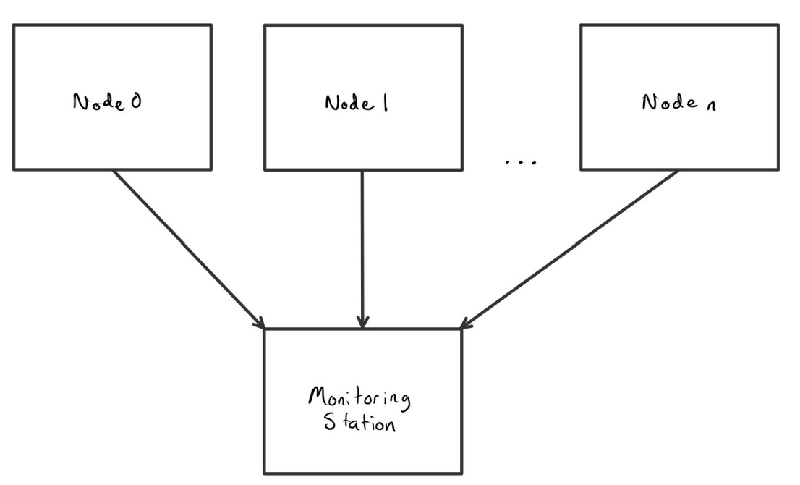
Images/L1diagramP2.jpg
