brandonhippe/Indoor-Air-Quality-Monitor/Images/Power_Consumption_vs_Sampling_Rate.png

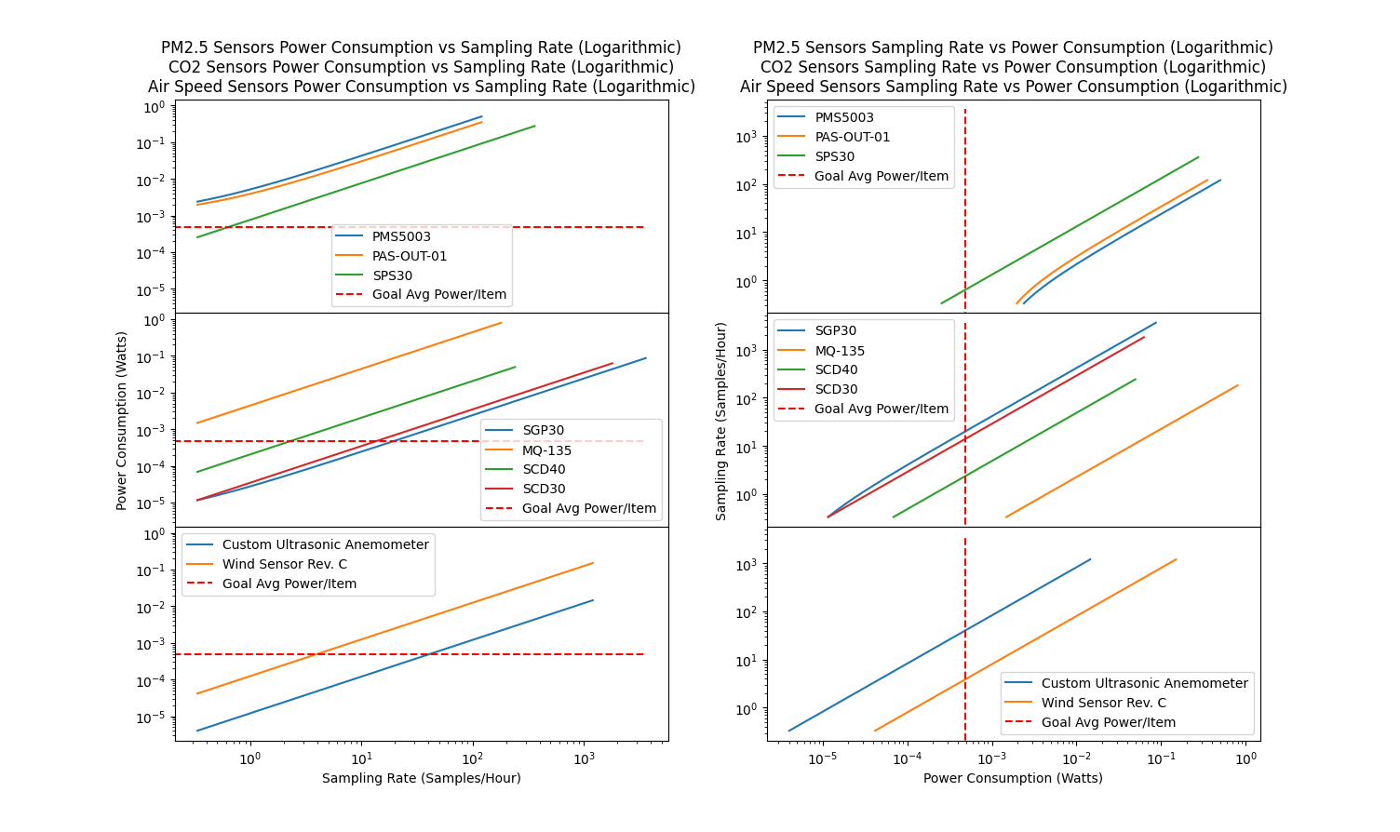
Images/Power_Consumption_vs_Sampling_Rate.png
