brandonhippe/Indoor-Air-Quality-Monitor/Images/springtimeline.jpg

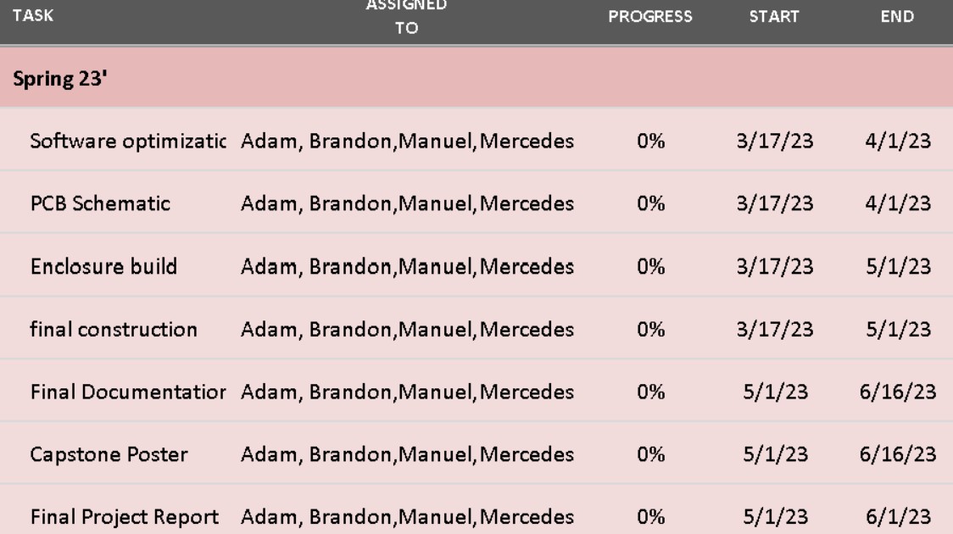
Images/springtimeline.jpg
