brandonhippe/Indoor-Air-Quality-Monitor/Images/WebBackground.jpg

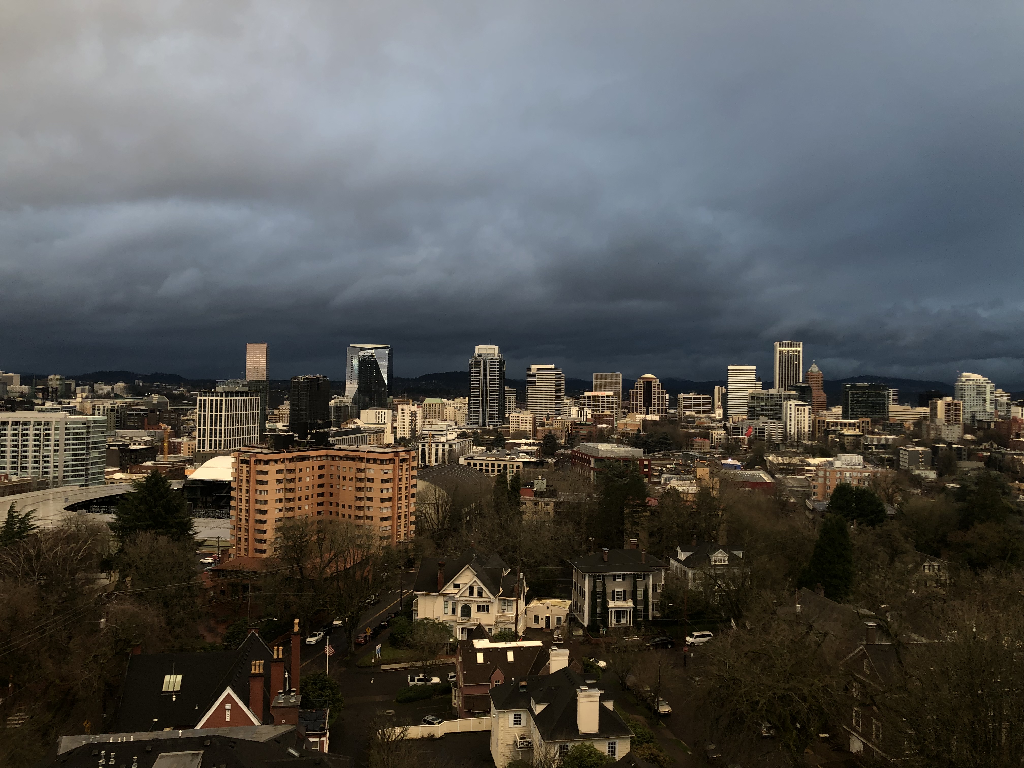
Images/WebBackground.jpg
