brandonhippe/Indoor-Air-Quality-Monitor/Documentation/Power testing/Power Consumption Test Results - Power Consumption - SCD41 PC.csv

Component | Name | Charge Consumed (On) | Period (minimum) | Typical Power Consumption (Off) | Notes
Micro Com | MSP430FR2355 + SmartMesh IP | 0 C | 0 s | 2.42 mW | On characteristics included with other component(s)
PM2.5 Sensor | Sensirion SPS30 | 2.76223 C | 30 s | 0 W
CO2 Sensor | Sensirion SCD41 | 199.227 mC | 15 s | 0 W
Anemometer | Custom Ultrasonic Anemometer | 17.0496 mC | 6 s | 0 W
