brandonhippe/Indoor-Air-Quality-Monitor/Documentation/Power testing/Power Consumption Test Results - Power Consumption.csv

Component | Name | Charge Consumed (On) | Period (minimum) | Typical Power Consumption (Off) | Notes
Micro Com | MSP430FR2355 + SmartMesh IP | 0 C | 0 s | 4.39 mW | On characteristics included with other component(s)
PM2.5 Sensor | Sensirion SPS30 | 5.04804 C | 30 s | 0 W
CO2 Sensor | Sensirion SCD41 | 2.07670 C | 20 s | 0 W
Anemometer | ClimateGuard Anemometer | 0 C | 20 s | 0 W | Included with other sensor(s)
