brandonhippe/Indoor-Air-Quality-Monitor/Documentation/Power testing/Power Consumption vs Sampling Rate Cropped.png

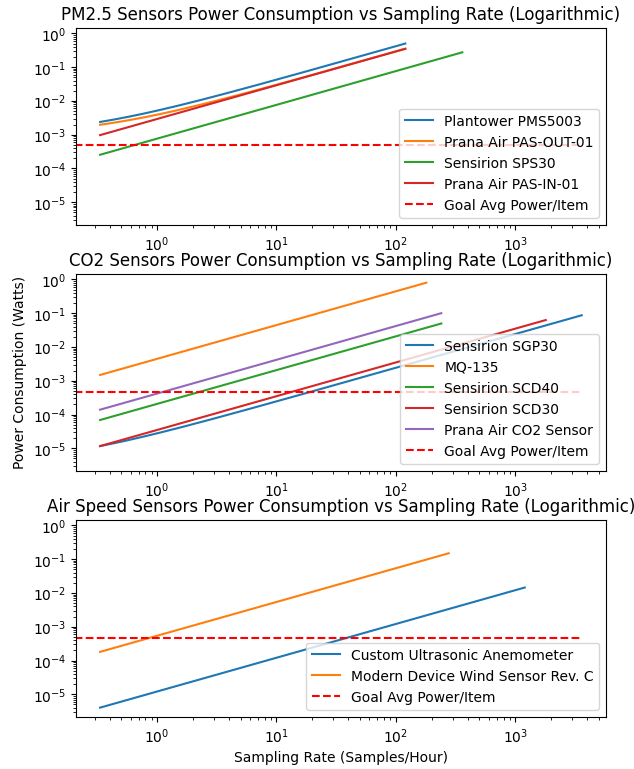
Documentation/Power testing/Power Consumption vs Sampling Rate Cropped.png
