brandonhippe/Indoor-Air-Quality-Monitor/Documentation/Power testing/Power Consumption vs Sampling Rate.png

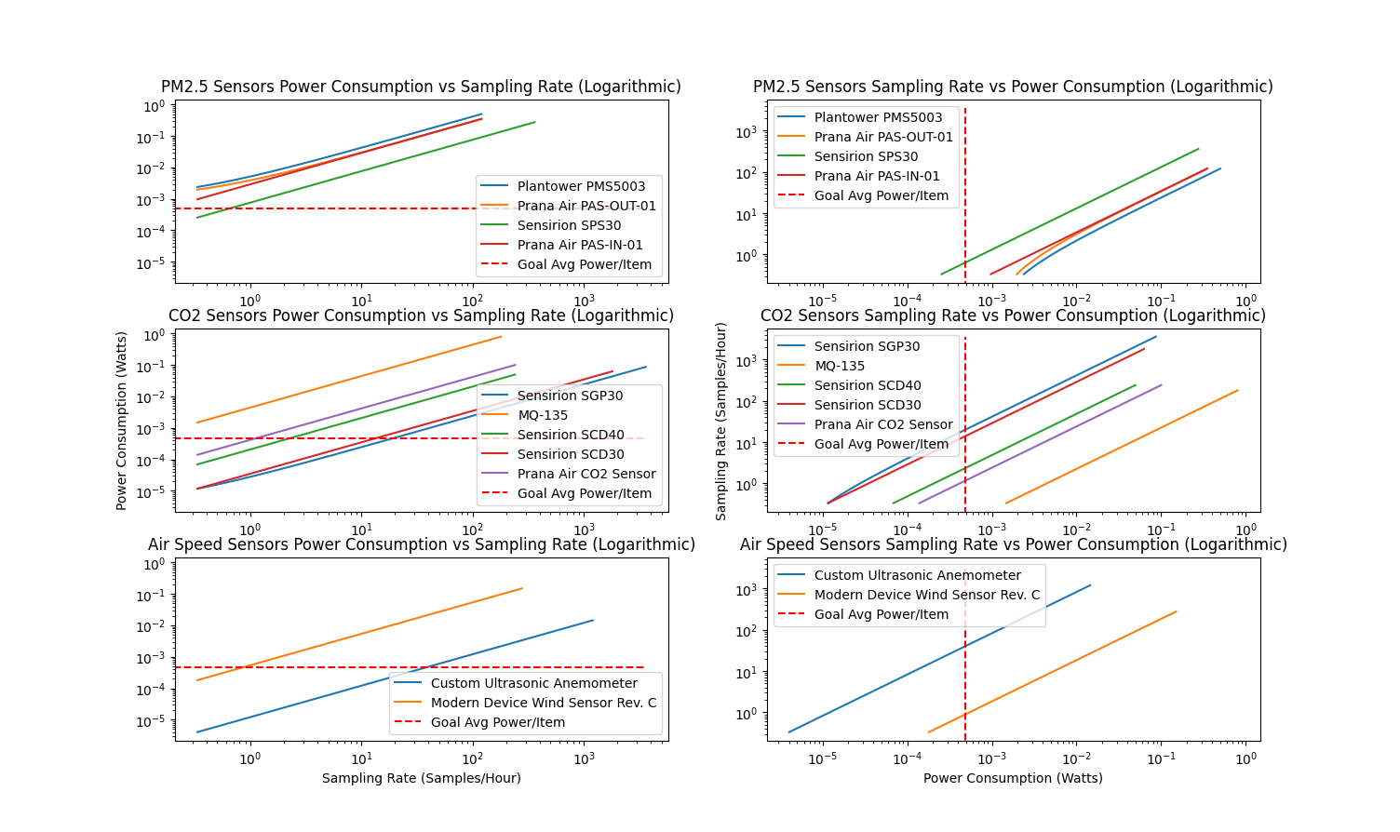
Documentation/Power testing/Power Consumption vs Sampling Rate.png
