brandonhippe/Indoor-Air-Quality-Monitor/Google Drive/Photos/Verify Button.png

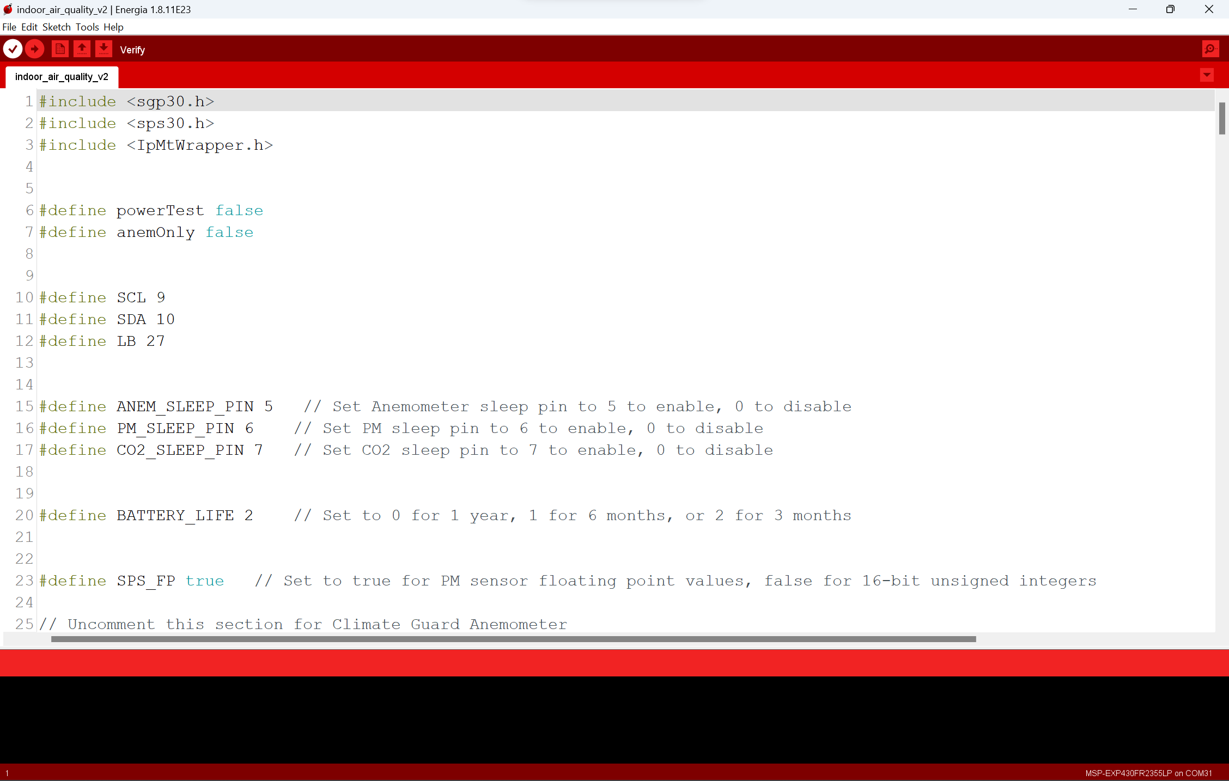
Google Drive/Photos/Verify Button.png
