brandonhippe/Indoor-Air-Quality-Monitor/Code/Sensor Code/sps30test/sps30test.ino

#include <sps30.h>
#include <Wire.h>


uint64_t time_ms;


SPS30 sps30;


void setup() {
  for (int i = 0; i < 40; i++) {
    digitalWrite(i, LOW);
    pinMode(i, OUTPUT);
  }

  Serial.begin(9600);
  Wire.begin();
  sps30.begin(millis());

  // Set time_ms and delay to start time
  time_ms = sps30.time_ms;
  while (millis() < time_ms);
}

void loop() {
  // Execute next function
  sps30.startNextFunc(millis());

  // Sleep until next function
  sleep(sps30.time_ms - millis());
}
